OrsoEric/robot-ros2-Industrious-Resonance/Images/2025-08-23_08_58_IMG_20250823_085845.jpg

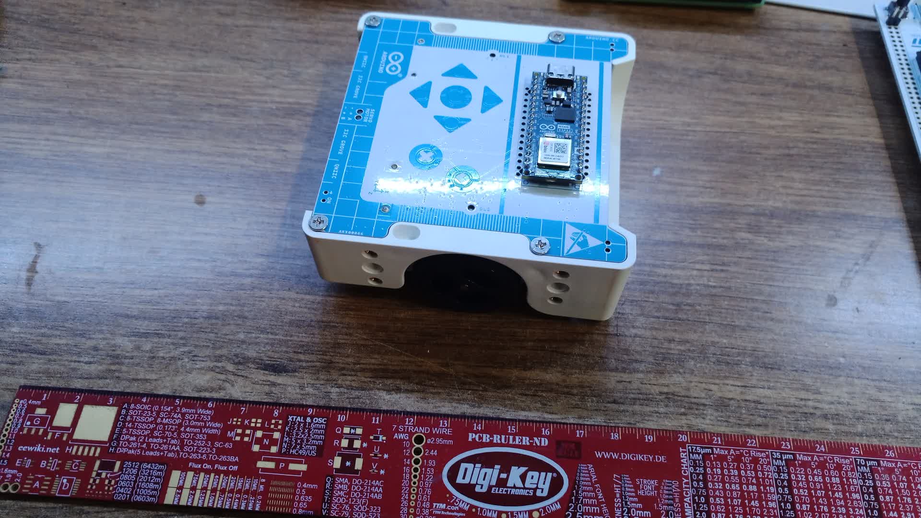
Images/2025-08-23_08_58_IMG_20250823_085845.jpg
