OrsoEric/robot-ros2-Industrious-Resonance/Images/2025-08-23_09_10_IMG_20250823_091027.jpg

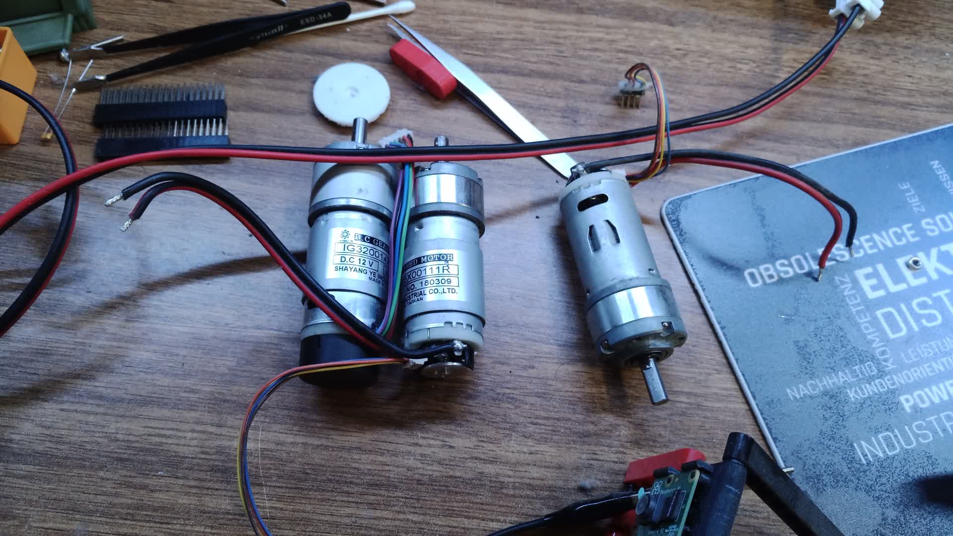
Images/2025-08-23_09_10_IMG_20250823_091027.jpg
