OrsoEric/robot-ros2-Industrious-Resonance/Images/2025-08-23_09_23_IMG_20250823_092340.jpg

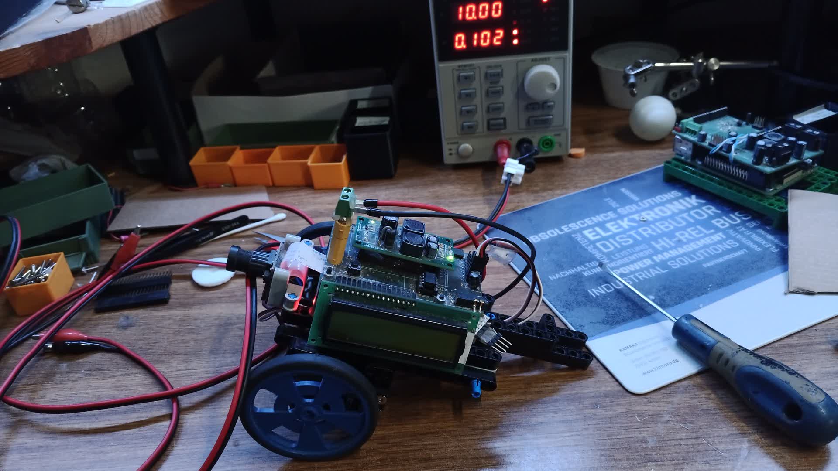
Images/2025-08-23_09_23_IMG_20250823_092340.jpg
