OrsoEric/robot-ros2-Industrious-Resonance/Images/2025-08-23_10_18_IMG_20250823_101841.jpg

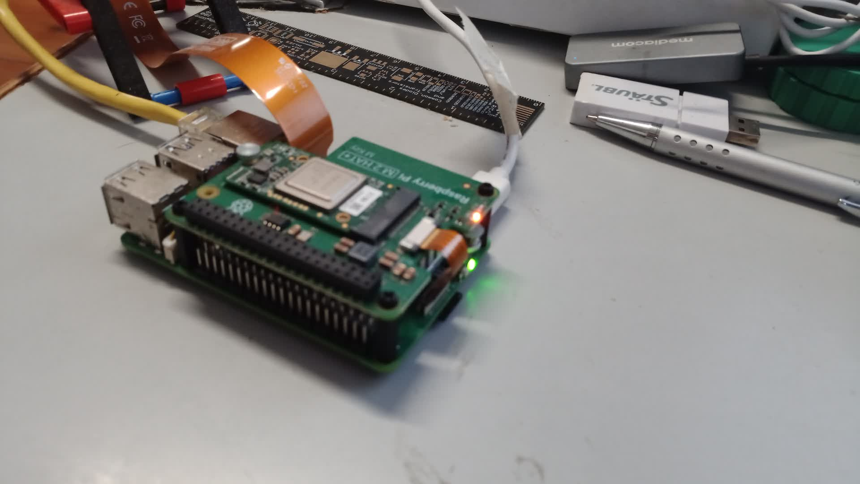
Images/2025-08-23_10_18_IMG_20250823_101841.jpg
