OrsoEric/robot-ros2-Industrious-Resonance/Images/2025-08-23_10_36_IMG_20250823_103639.jpg

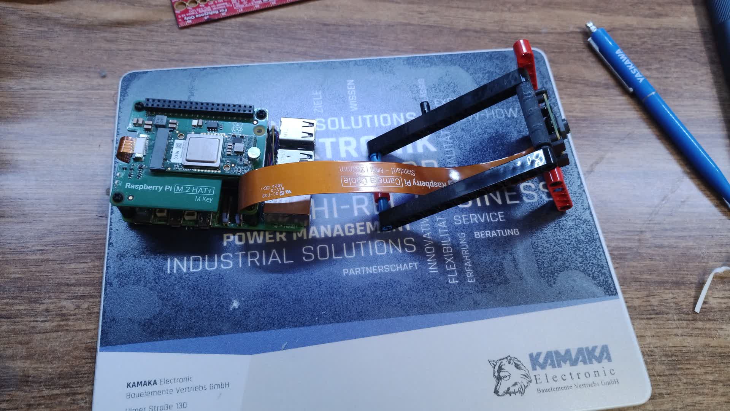
Images/2025-08-23_10_36_IMG_20250823_103639.jpg
