OrsoEric/robot-ros2-Industrious-Resonance/Images/2025-08-23_10_53_IMG_20250823_105316.jpg

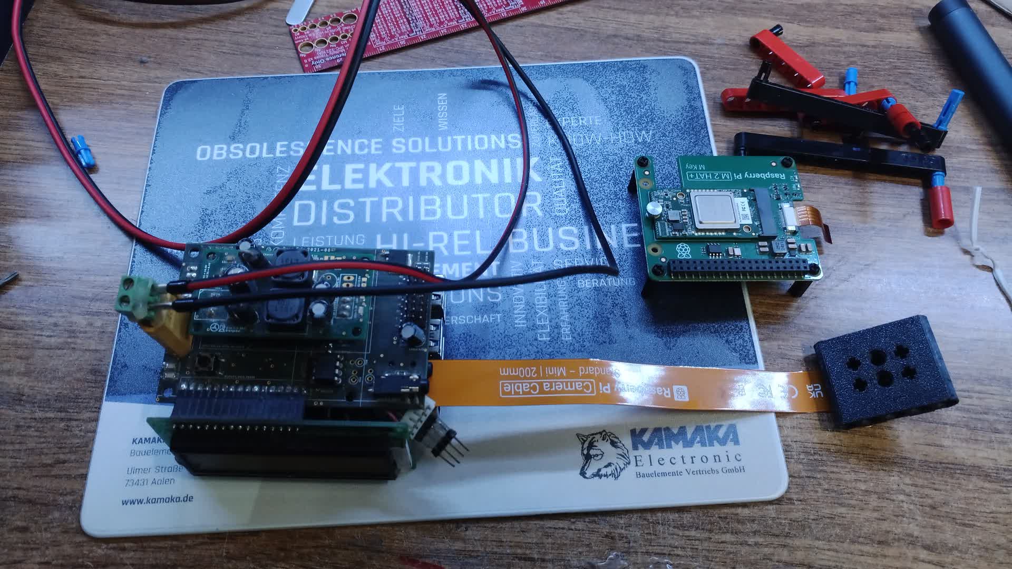
Images/2025-08-23_10_53_IMG_20250823_105316.jpg
