OrsoEric/robot-ros2-Industrious-Resonance/Images/2025-08-25_19_26_IMG_20250825_192647.jpg

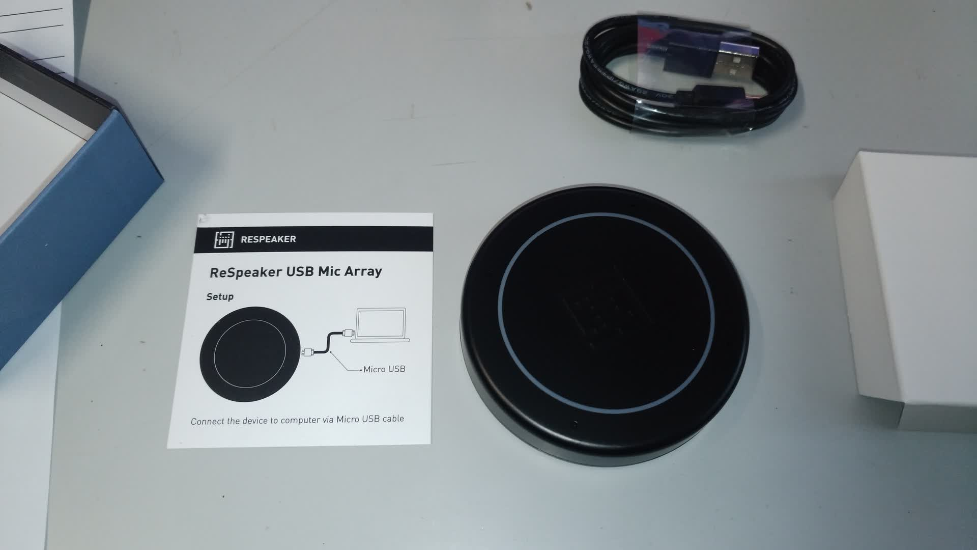
Images/2025-08-25_19_26_IMG_20250825_192647.jpg
