OrsoEric/robot-ros2-Industrious-Resonance/Images/2025-08-27_08_57_IMG_20250827_085710.jpg

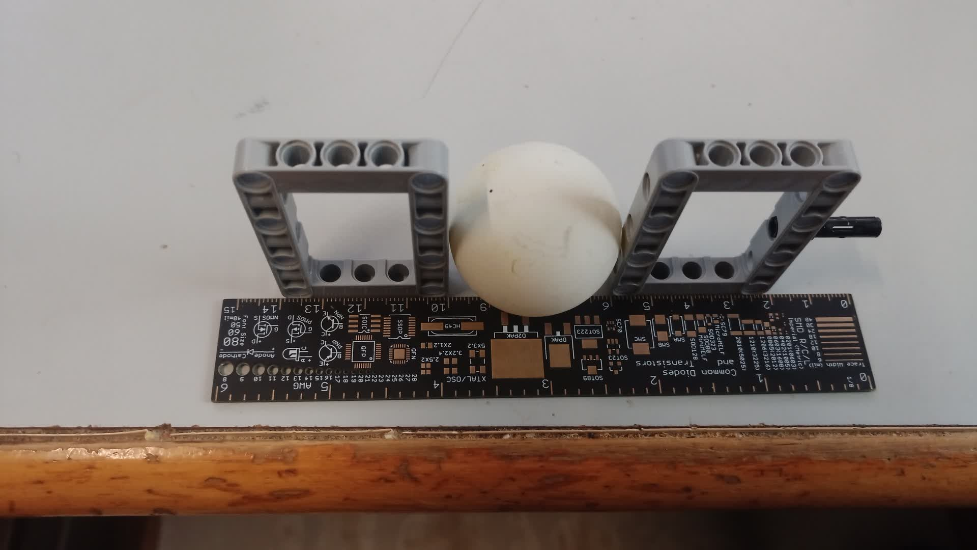
Images/2025-08-27_08_57_IMG_20250827_085710.jpg
