OrsoEric/robot-ros2-Industrious-Resonance/Images/2025-08-27_13_16_IMG_20250827_131654.jpg

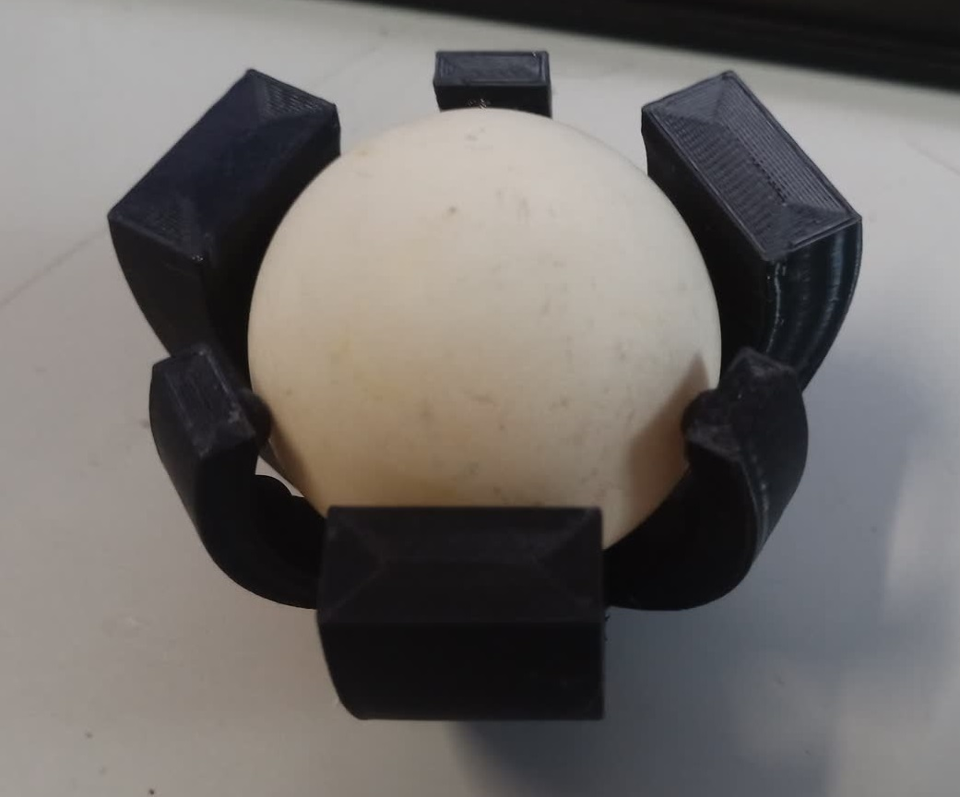
Images/2025-08-27_13_16_IMG_20250827_131654.jpg
