OrsoEric/robot-ros2-Industrious-Resonance/Images/2025-08-27_14_06_IMG_20250827_140644.jpg

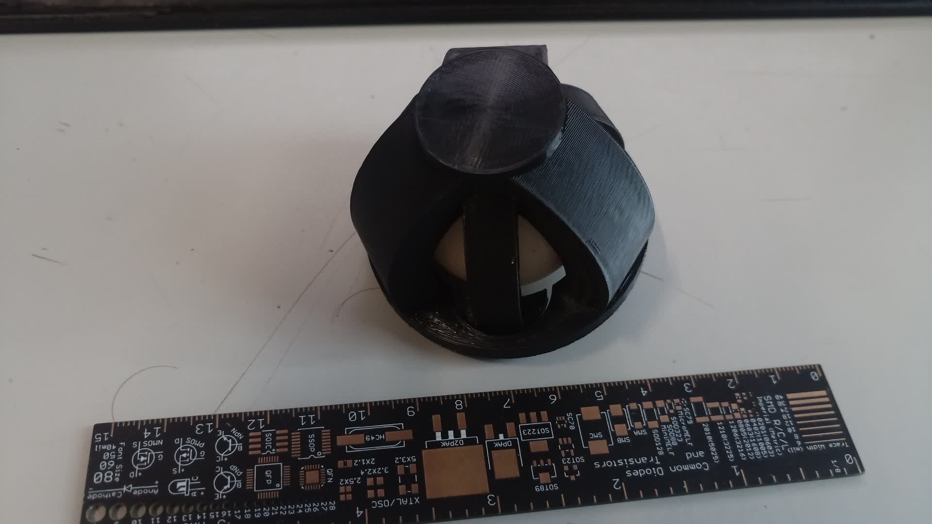
Images/2025-08-27_14_06_IMG_20250827_140644.jpg
