OrsoEric/robot-ros2-Industrious-Resonance/Images/2025-08-27_16_06_IMG_20250827_160652.jpg

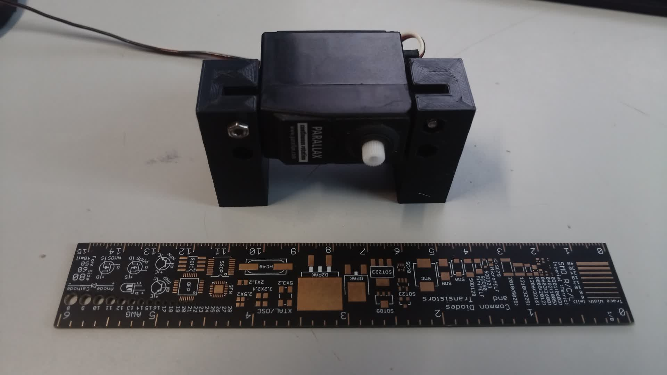
Images/2025-08-27_16_06_IMG_20250827_160652.jpg
