OrsoEric/robot-ros2-Industrious-Resonance/Images/2025-08-27_17_10_IMG_20250827_171056.jpg

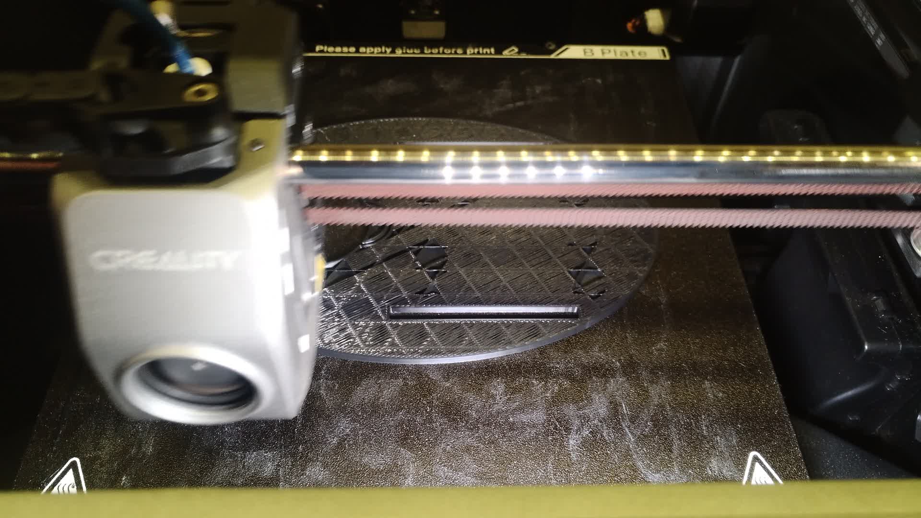
Images/2025-08-27_17_10_IMG_20250827_171056.jpg
