OrsoEric/robot-ros2-Industrious-Resonance/Images/2025-08-27_17_11_IMG_20250827_171102.jpg

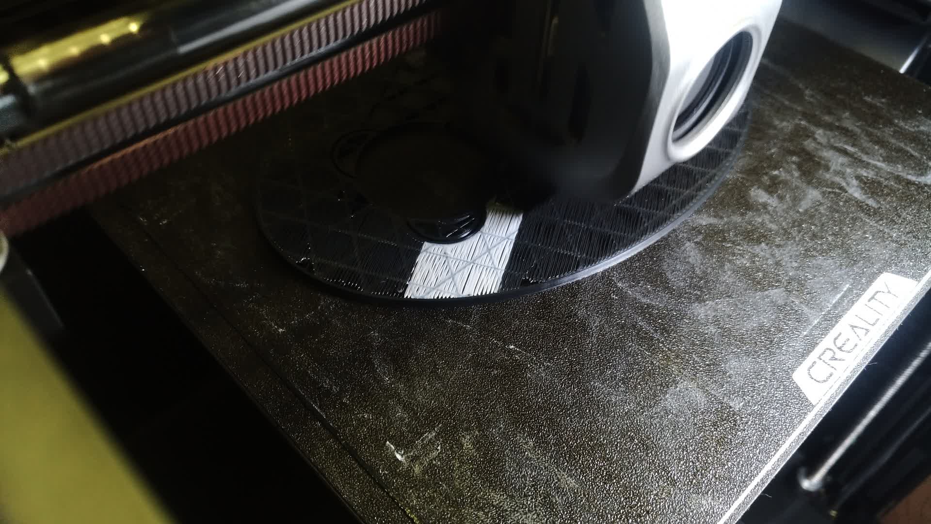
Images/2025-08-27_17_11_IMG_20250827_171102.jpg
