OrsoEric/robot-ros2-Industrious-Resonance/Images/2025-11-06_13_21_IMG_20251106_132114.jpg

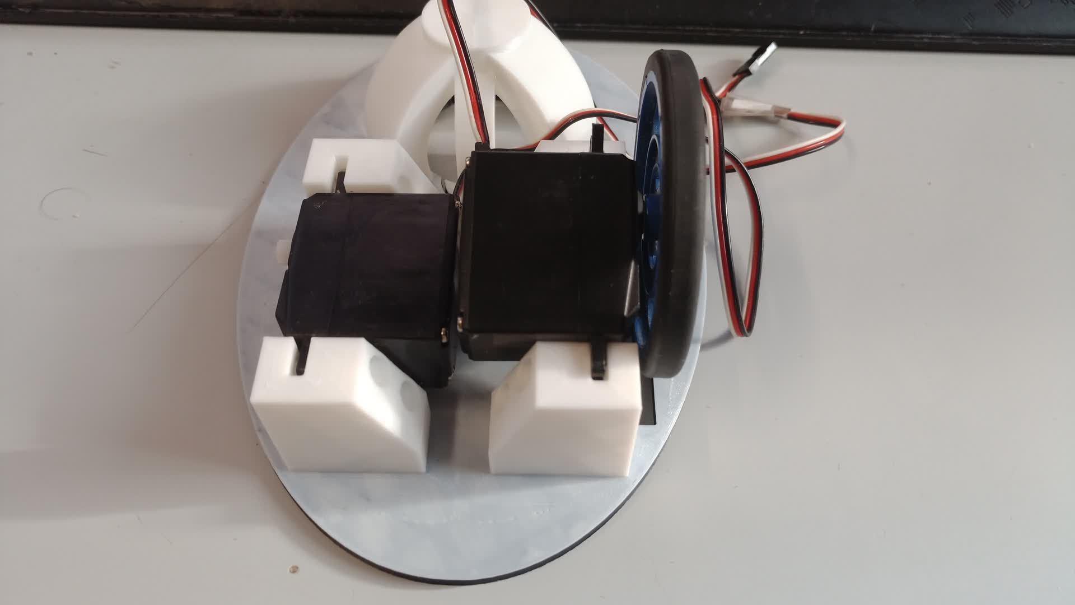
Images/2025-11-06_13_21_IMG_20251106_132114.jpg
