OrsoEric/robot-ros2-Industrious-Resonance/Images/2025-11-06_17_39_IMG_20251106_173956.jpg

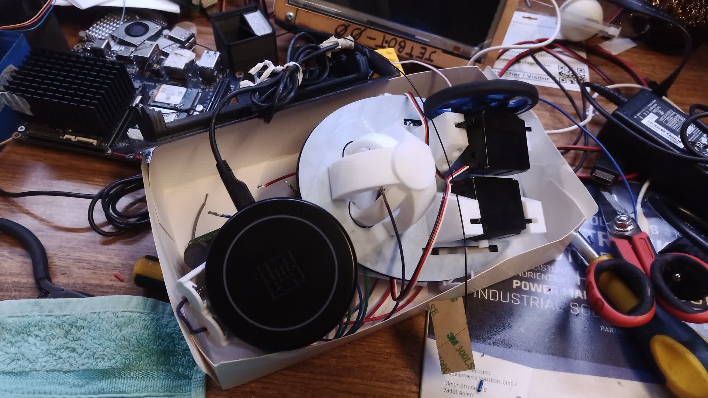
Images/2025-11-06_17_39_IMG_20251106_173956.jpg
