OrsoEric/robot-ros2-Industrious-Resonance/Images/2025-11-08_11_53_IMG_20251108_115348.jpg

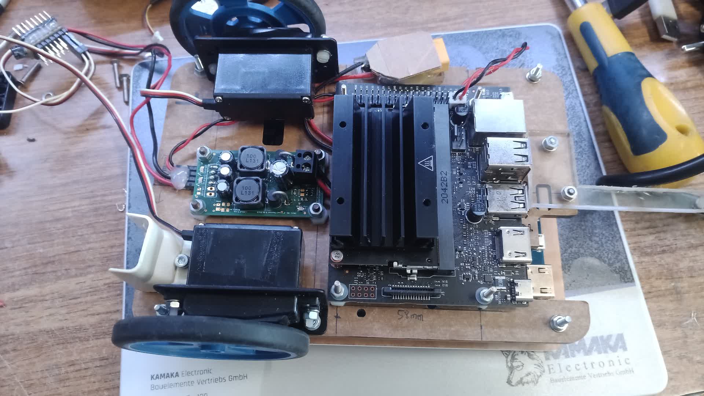
Images/2025-11-08_11_53_IMG_20251108_115348.jpg
