OrsoEric/robot-ros2-Industrious-Resonance/Images/2025-11-08_12_08_IMG_20251108_120841.jpg

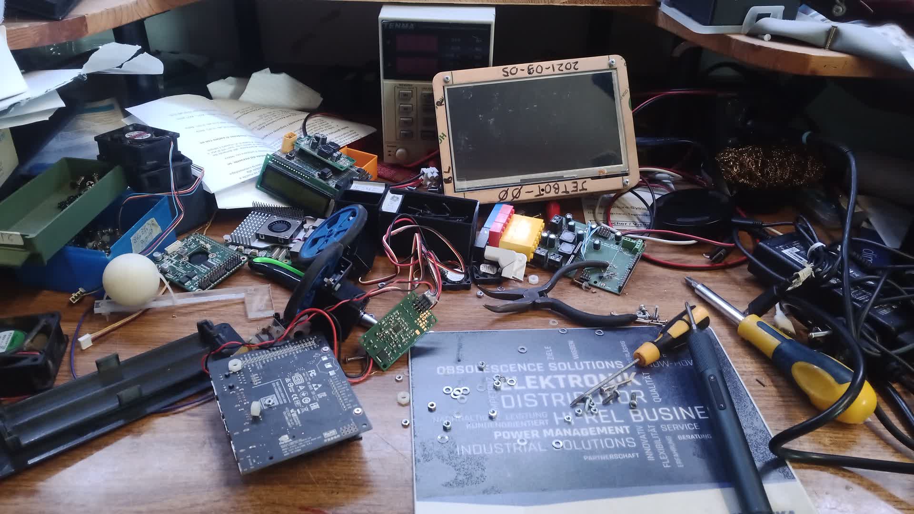
Images/2025-11-08_12_08_IMG_20251108_120841.jpg
