OrsoEric/robot-ros2-Industrious-Resonance/Images/2025-11-08_12_09_IMG_20251108_120904.jpg

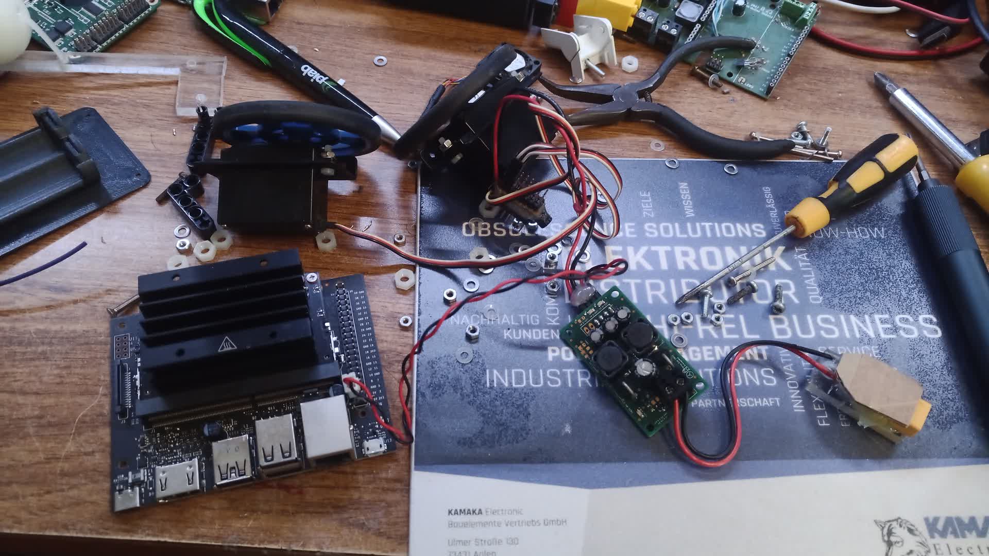
Images/2025-11-08_12_09_IMG_20251108_120904.jpg
