OrsoEric/robot-ros2-Industrious-Resonance/Images/2025-11-08_12_16_IMG_20251108_121650.jpg

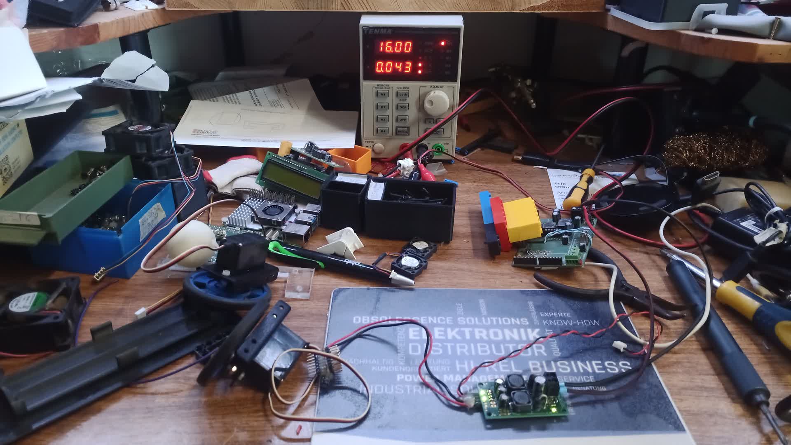
Images/2025-11-08_12_16_IMG_20251108_121650.jpg
