OrsoEric/robot-ros2-Industrious-Resonance/Images/2025-11-08_12_21_IMG_20251108_122142.jpg

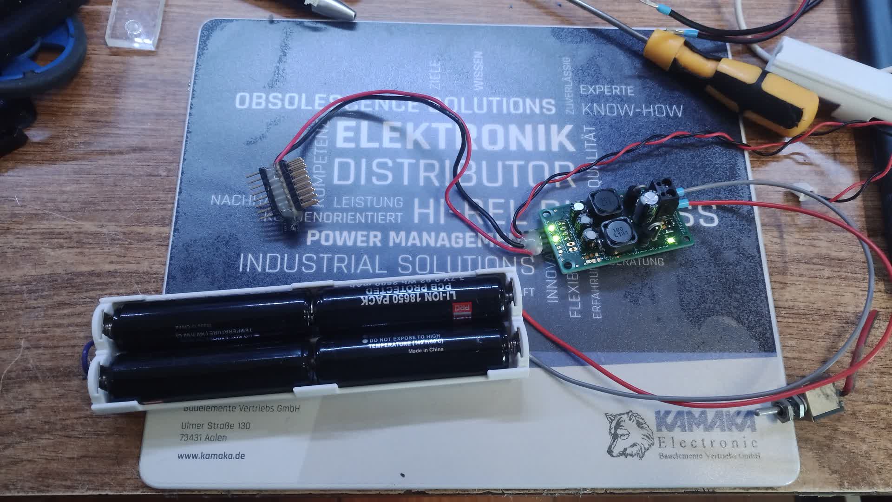
Images/2025-11-08_12_21_IMG_20251108_122142.jpg
