OrsoEric/robot-ros2-Industrious-Resonance/Images/2025-11-08_21_04_IMG_20251108_210415.jpg

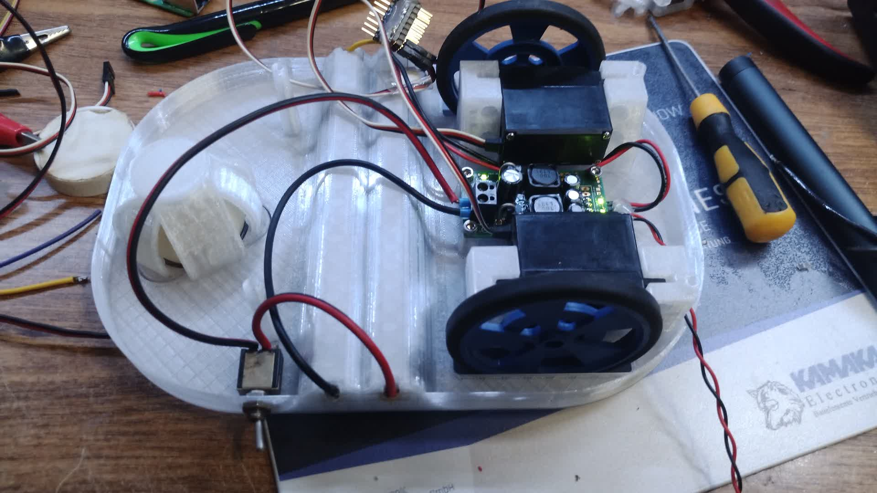
Images/2025-11-08_21_04_IMG_20251108_210415.jpg
