OrsoEric/robot-ros2-Industrious-Resonance/Images/2025-11-08_21_04_IMG_20251108_210431.jpg

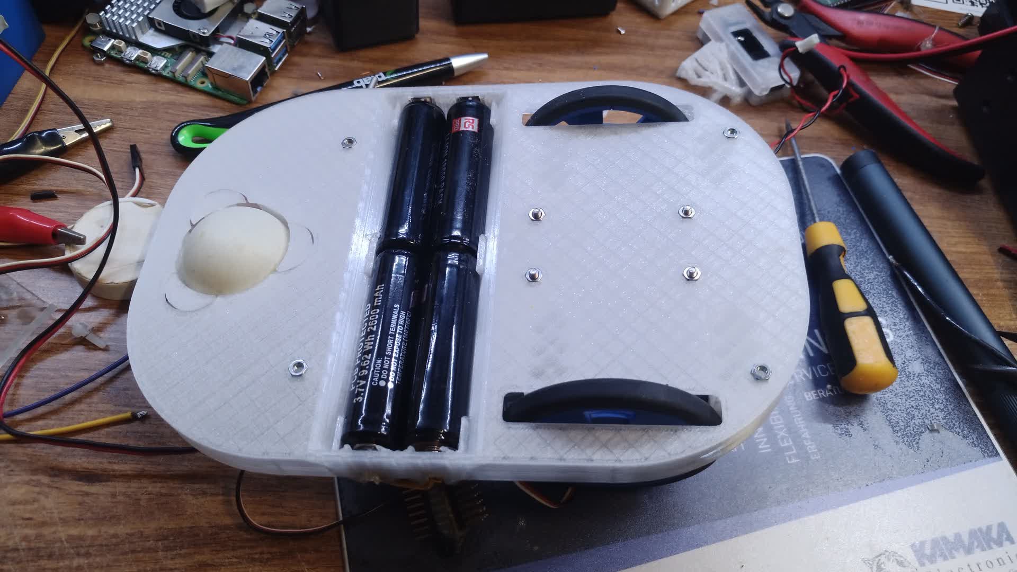
Images/2025-11-08_21_04_IMG_20251108_210431.jpg
