OrsoEric/robot-ros2-Industrious-Resonance/Images/2025-11-09_09_07_IMG_20251109_090746.jpg

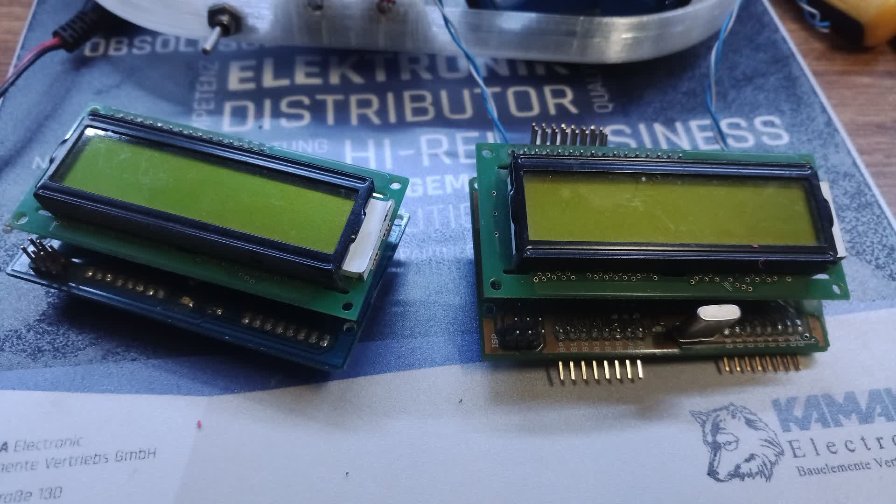
Images/2025-11-09_09_07_IMG_20251109_090746.jpg
