OrsoEric/robot-ros2-Industrious-Resonance/Images/2025-11-09_09_24_IMG_20251109_092415.jpg

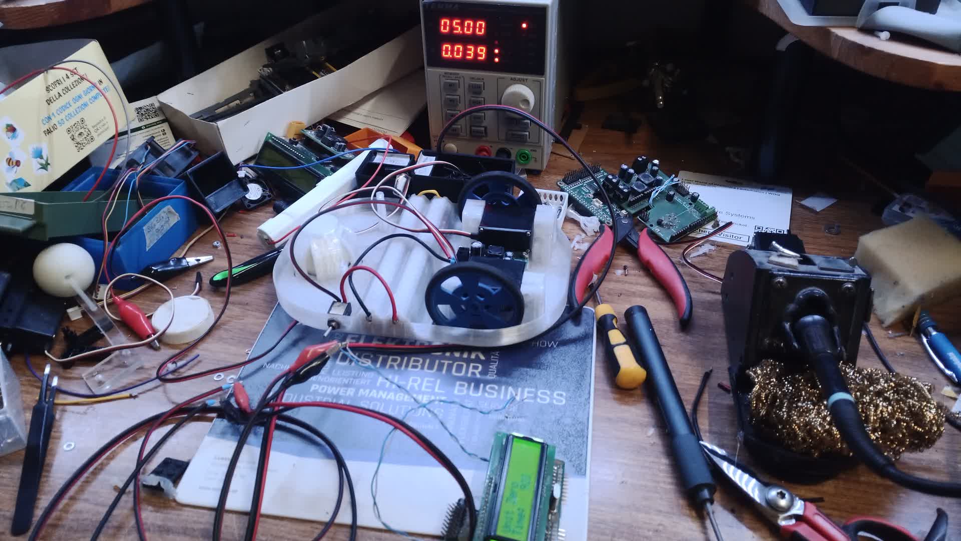
Images/2025-11-09_09_24_IMG_20251109_092415.jpg
