OrsoEric/robot-ros2-Industrious-Resonance/Images/2025-11-09_09_36_IMG_20251109_093618.jpg

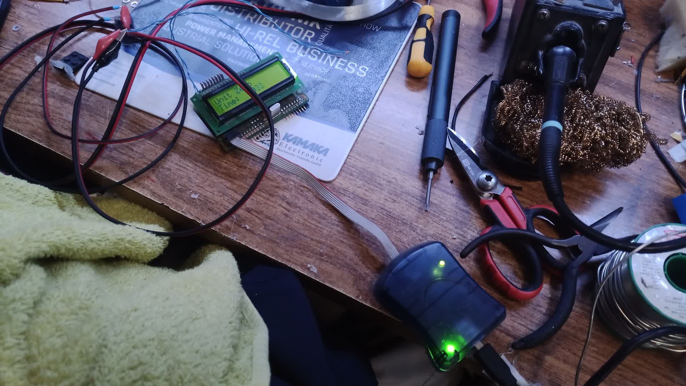
Images/2025-11-09_09_36_IMG_20251109_093618.jpg
