OrsoEric/robot-ros2-Industrious-Resonance/Images/2025-11-09_09_51_IMG_20251109_095159.jpg

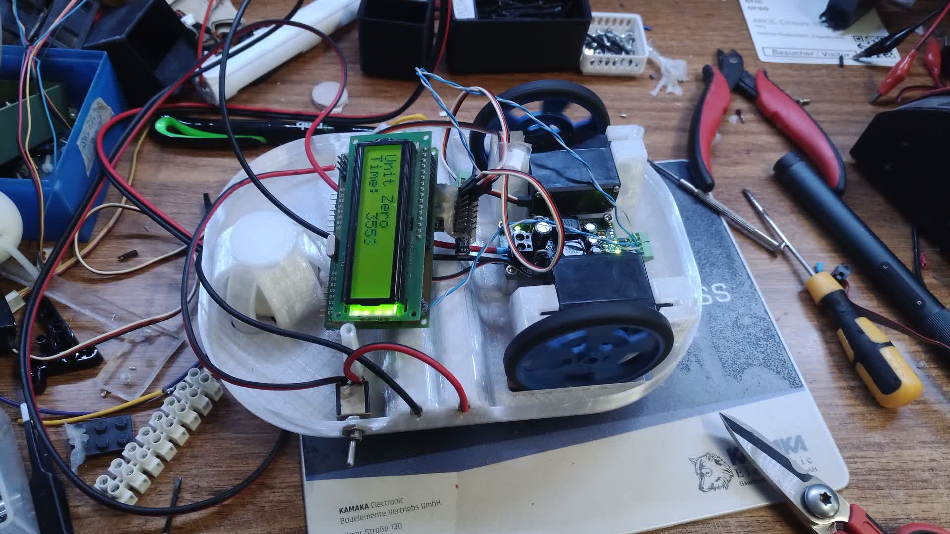
Images/2025-11-09_09_51_IMG_20251109_095159.jpg
