OrsoEric/robot-ros2-Industrious-Resonance/Images/2025-11-09_11_59_IMG_20251109_115955.jpg

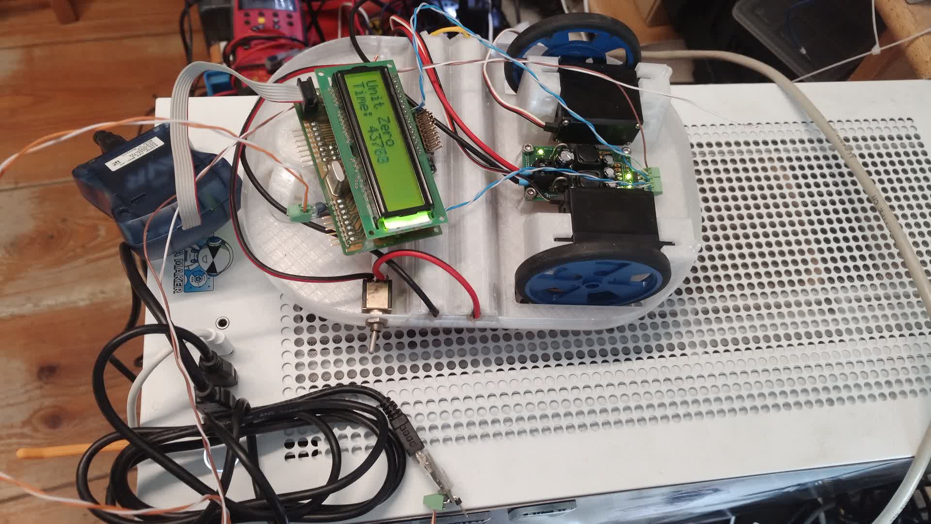
Images/2025-11-09_11_59_IMG_20251109_115955.jpg
