OrsoEric/robot-ros2-Industrious-Resonance/Images/2025-11-09_13_45_IMG_20251109_134523.jpg

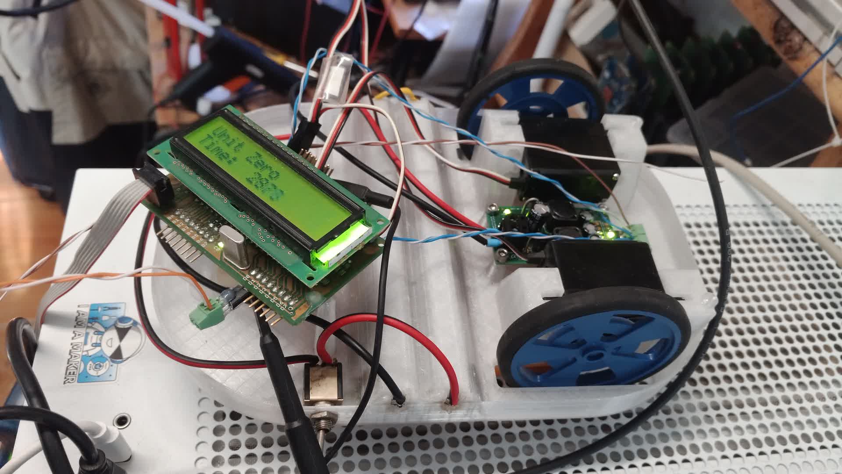
Images/2025-11-09_13_45_IMG_20251109_134523.jpg
