OrsoEric/robot-ros2-Industrious-Resonance/Images/IMG_20250823_113036.jpg

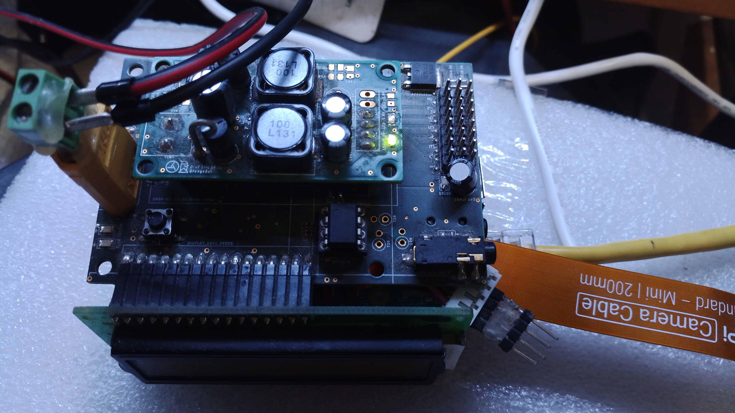
Images/IMG_20250823_113036.jpg
