OrsoEric/robot-ros2-Industrious-Resonance/Images/Screenshot 2025-08-27 132716.png

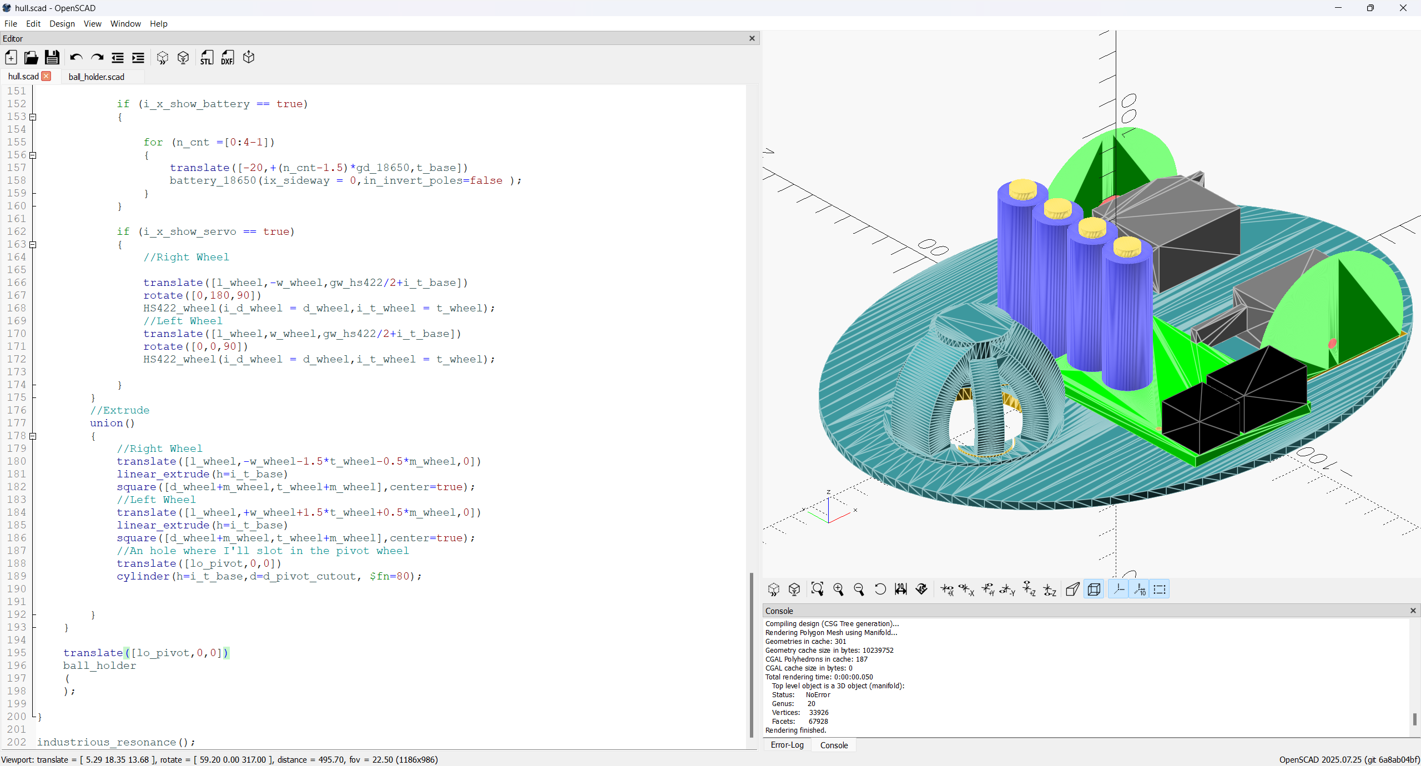
Images/Screenshot 2025-08-27 132716.png
