OrsoEric/robot-ros2-Industrious-Resonance/Images/Screenshot 2025-10-25 123542.png

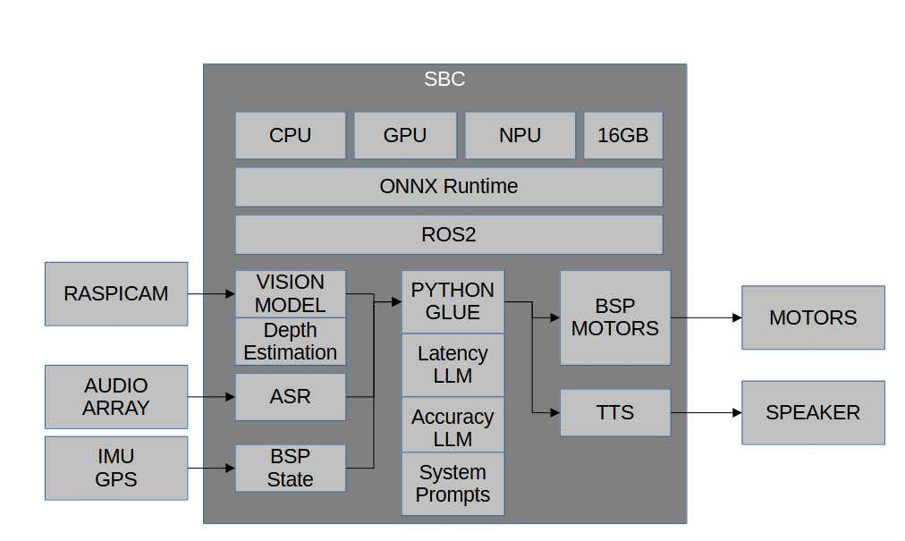
Images/Screenshot 2025-10-25 123542.png
