OrsoEric/robot-ros2-Industrious-Resonance/Images/Screenshot 2025-11-02 103534.png

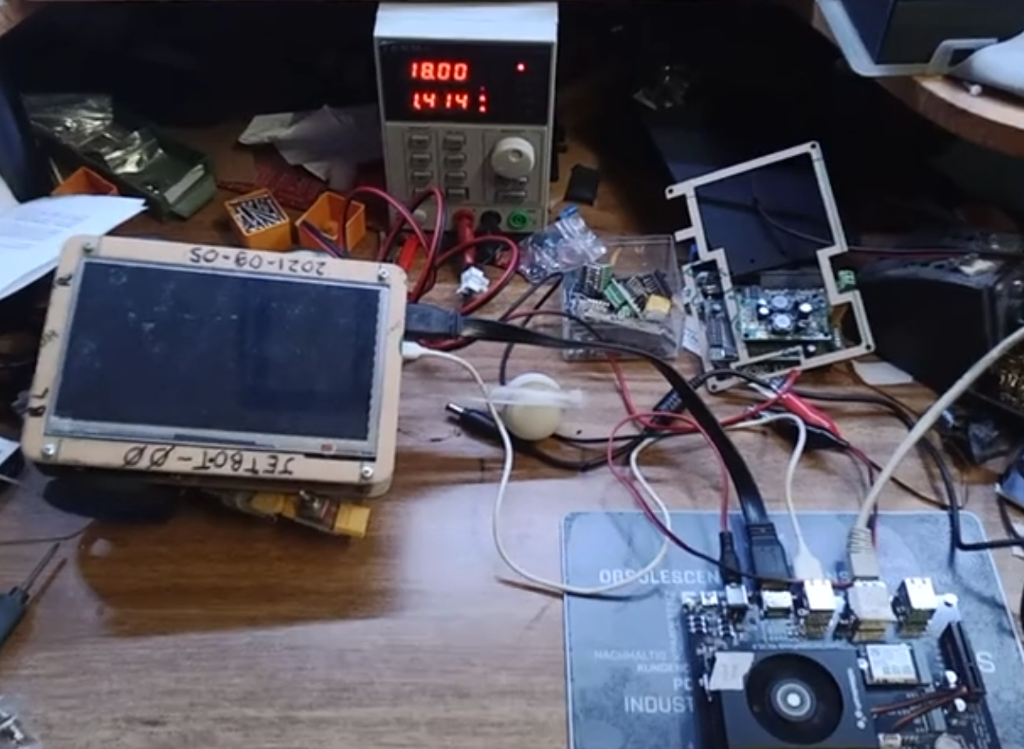
Images/Screenshot 2025-11-02 103534.png
