OrsoEric/robot-ros2-Industrious-Resonance/Images/Screenshot 2025-11-06 130414.png

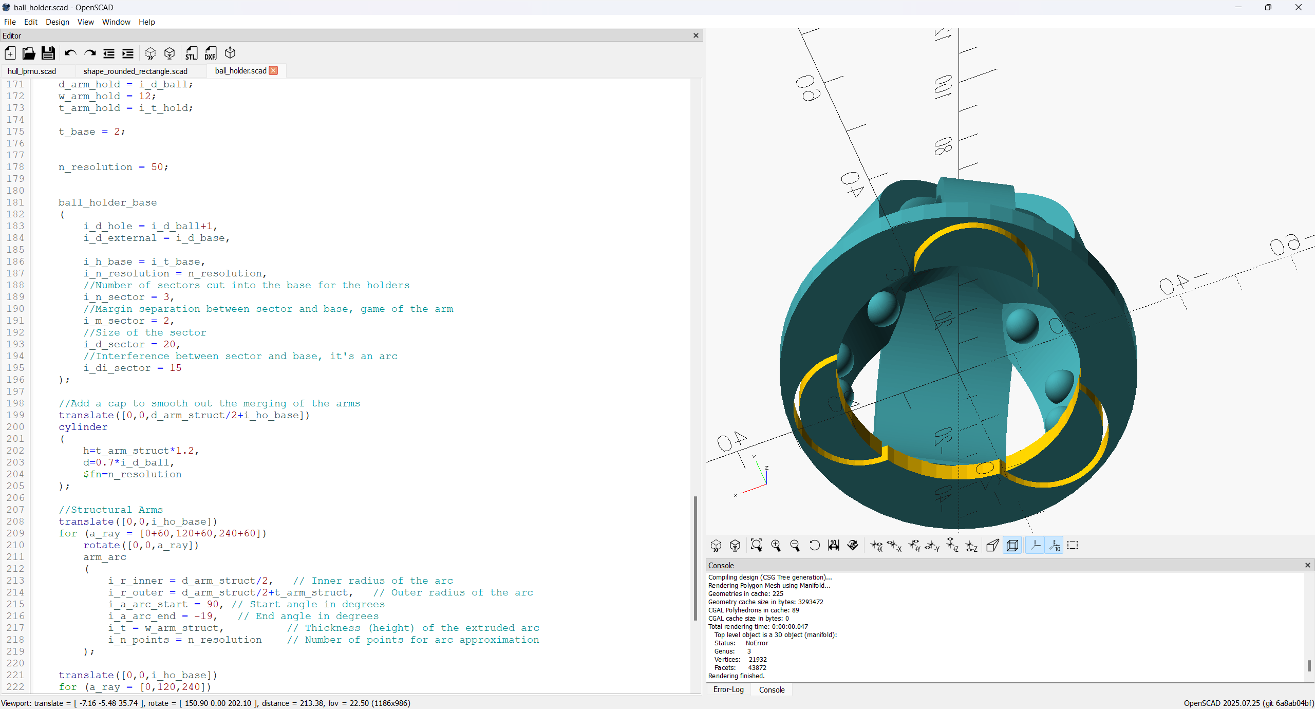
Images/Screenshot 2025-11-06 130414.png
