OrsoEric/robot-ros2-Industrious-Resonance/Images/Screenshot 2025-11-06 132450.png

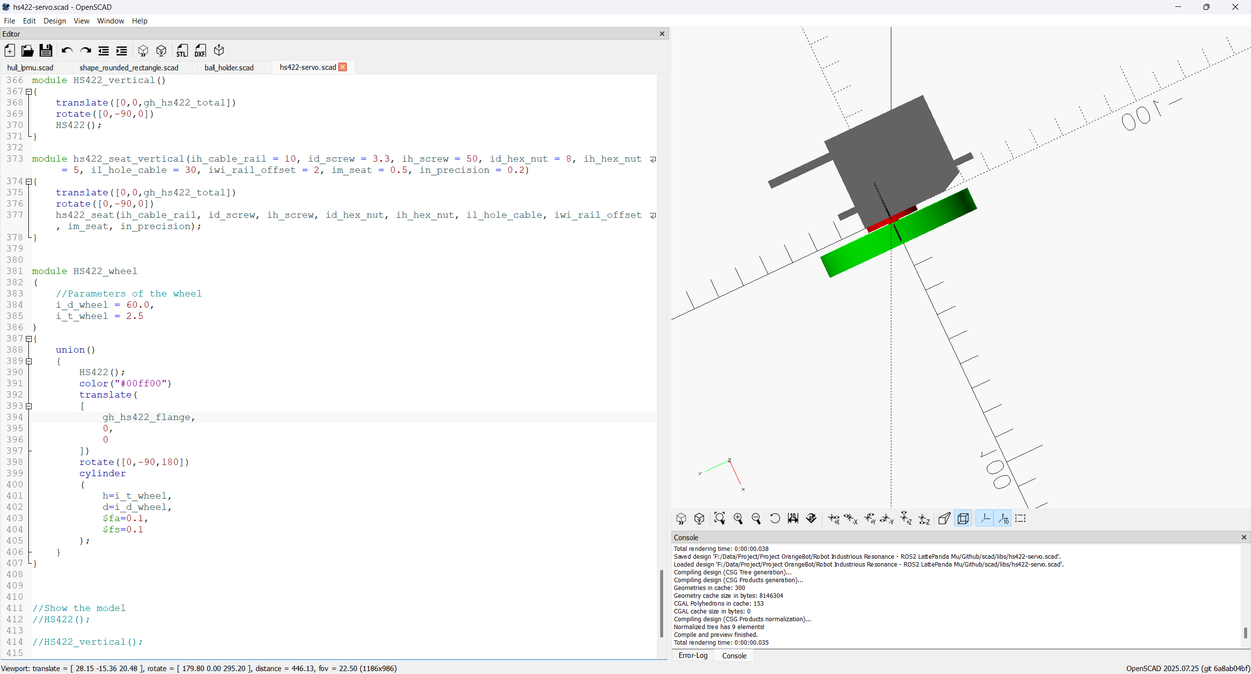
Images/Screenshot 2025-11-06 132450.png
