OrsoEric/robot-ros2-Industrious-Resonance/Images/Screenshot 2025-11-08 085803.png

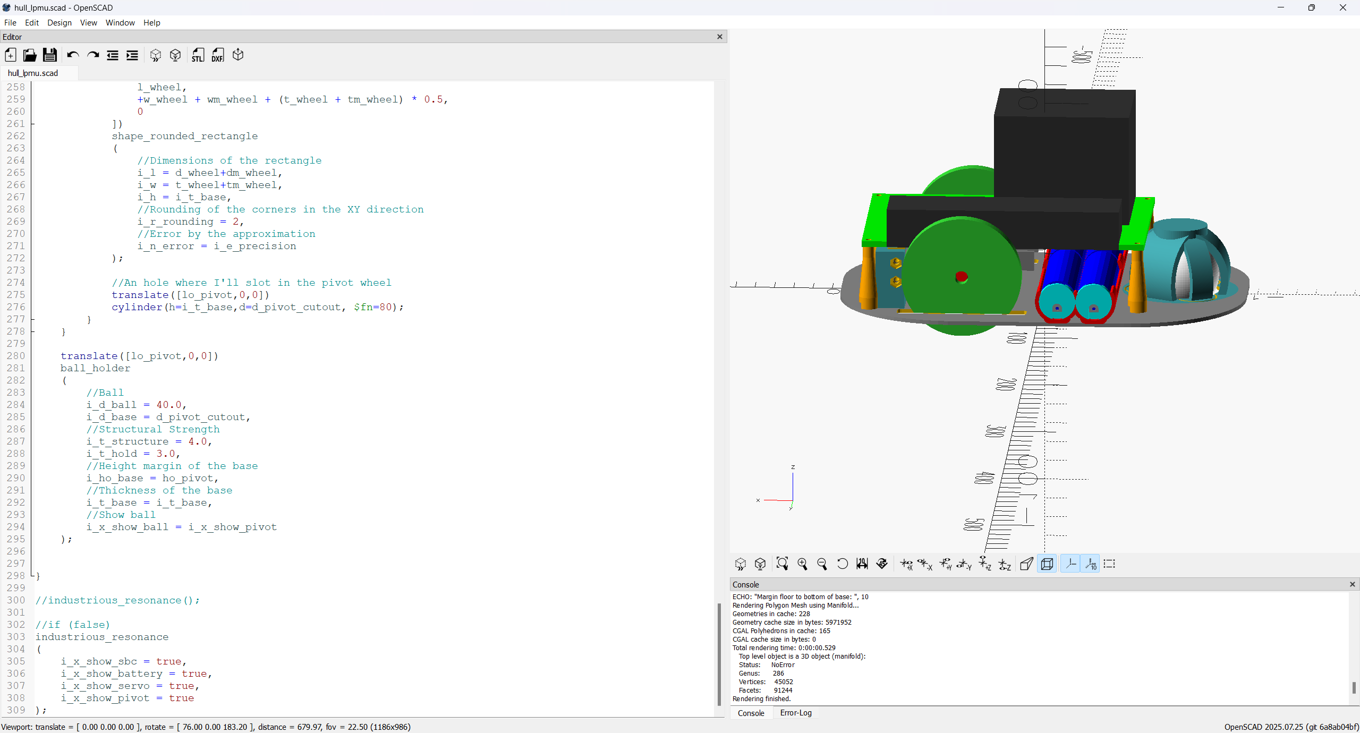
Images/Screenshot 2025-11-08 085803.png
