OrsoEric/robot-ros2-Industrious-Resonance/Images/Screenshot 2025-11-08 110413.png

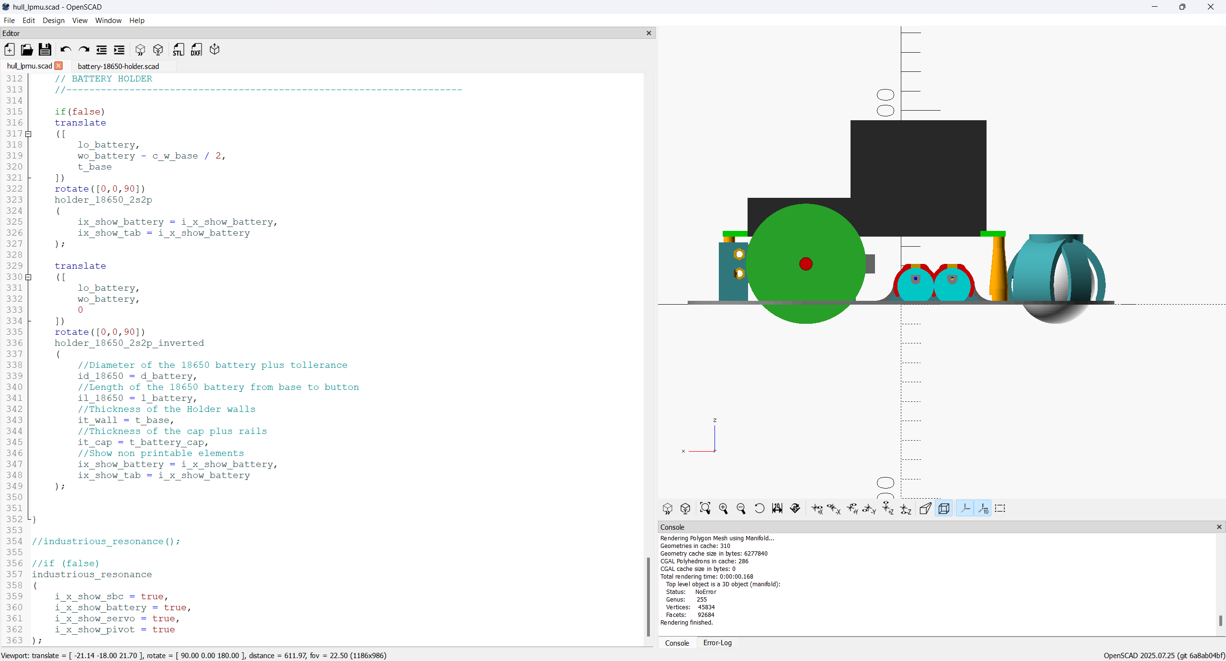
Images/Screenshot 2025-11-08 110413.png
