OrsoEric/robot-ros2-Industrious-Resonance/Images/Screenshot 2025-11-08 111840.png

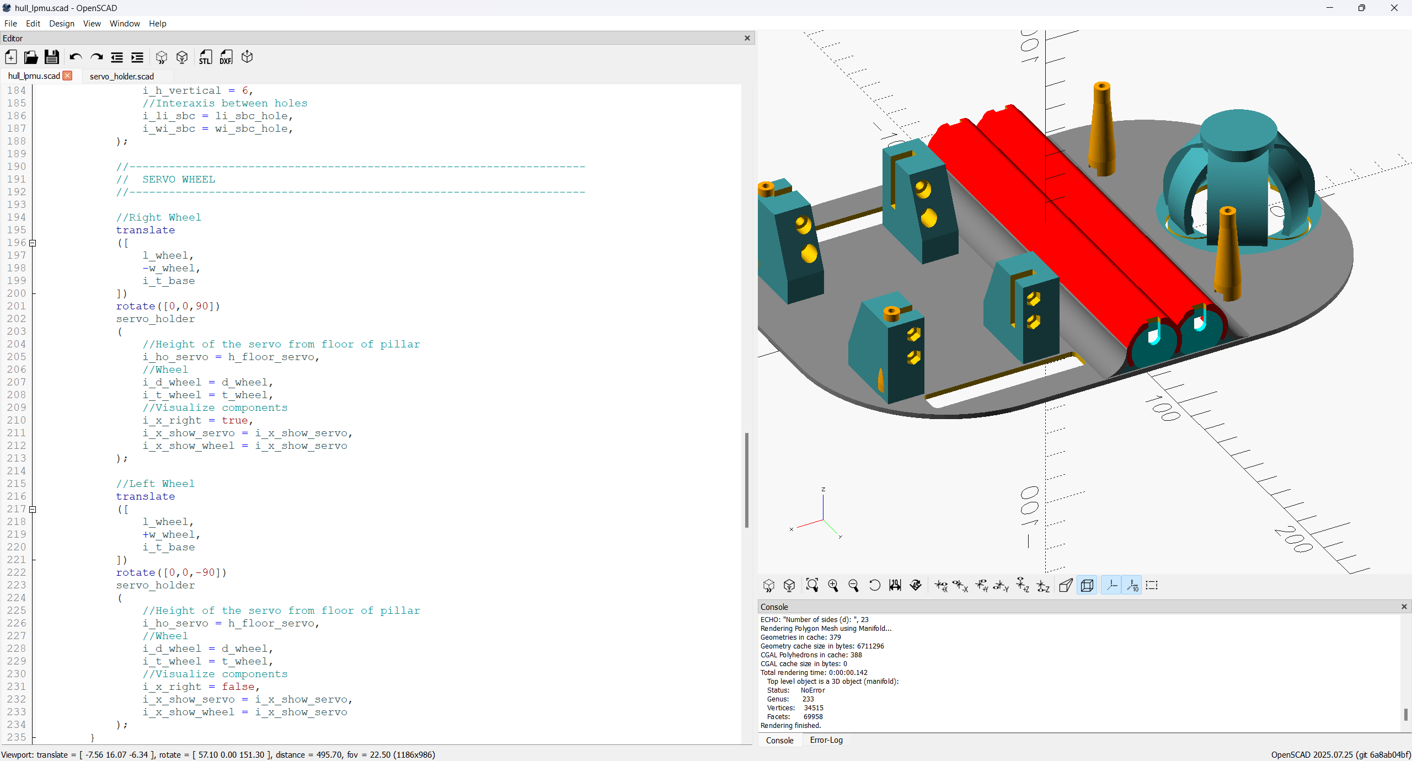
Images/Screenshot 2025-11-08 111840.png
