OrsoEric/robot-ros2-Industrious-Resonance/Images/Screenshot 2025-11-08 131336.png

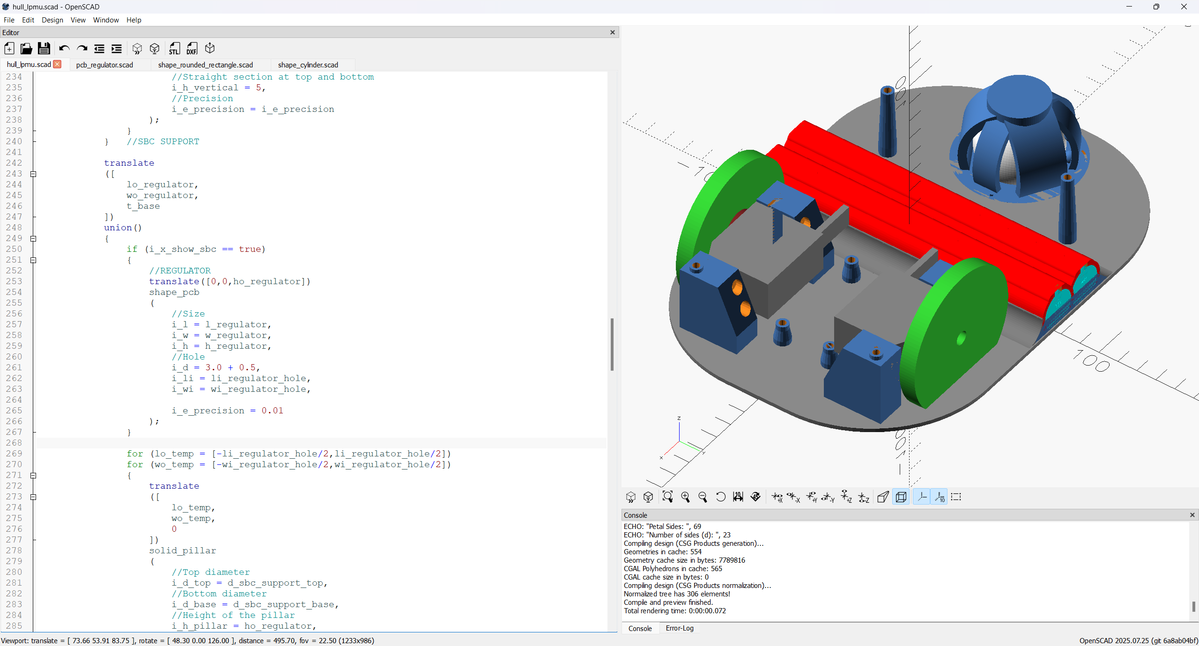
Images/Screenshot 2025-11-08 131336.png
