OrsoEric/robot-ros2-Industrious-Resonance/Images/Screenshot 2025-11-08 135248.png

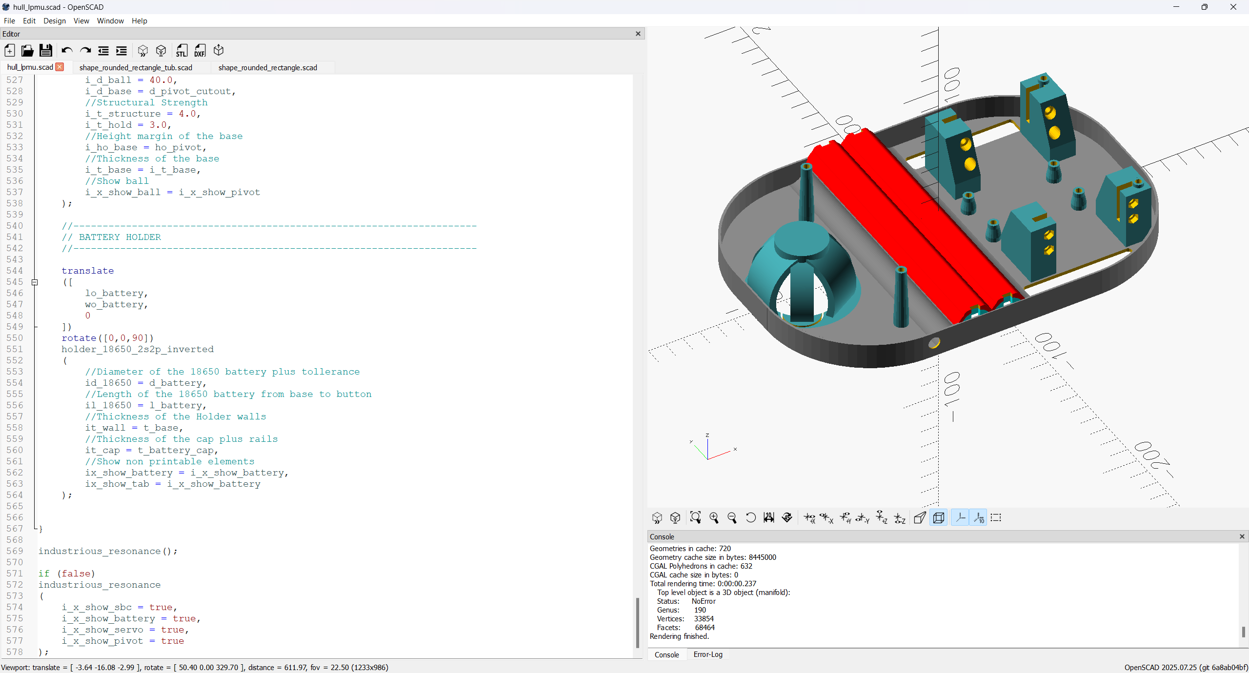
Images/Screenshot 2025-11-08 135248.png
