OrsoEric/robot-ros2-Industrious-Resonance/Images/Screenshot 2025-11-09 075105.png

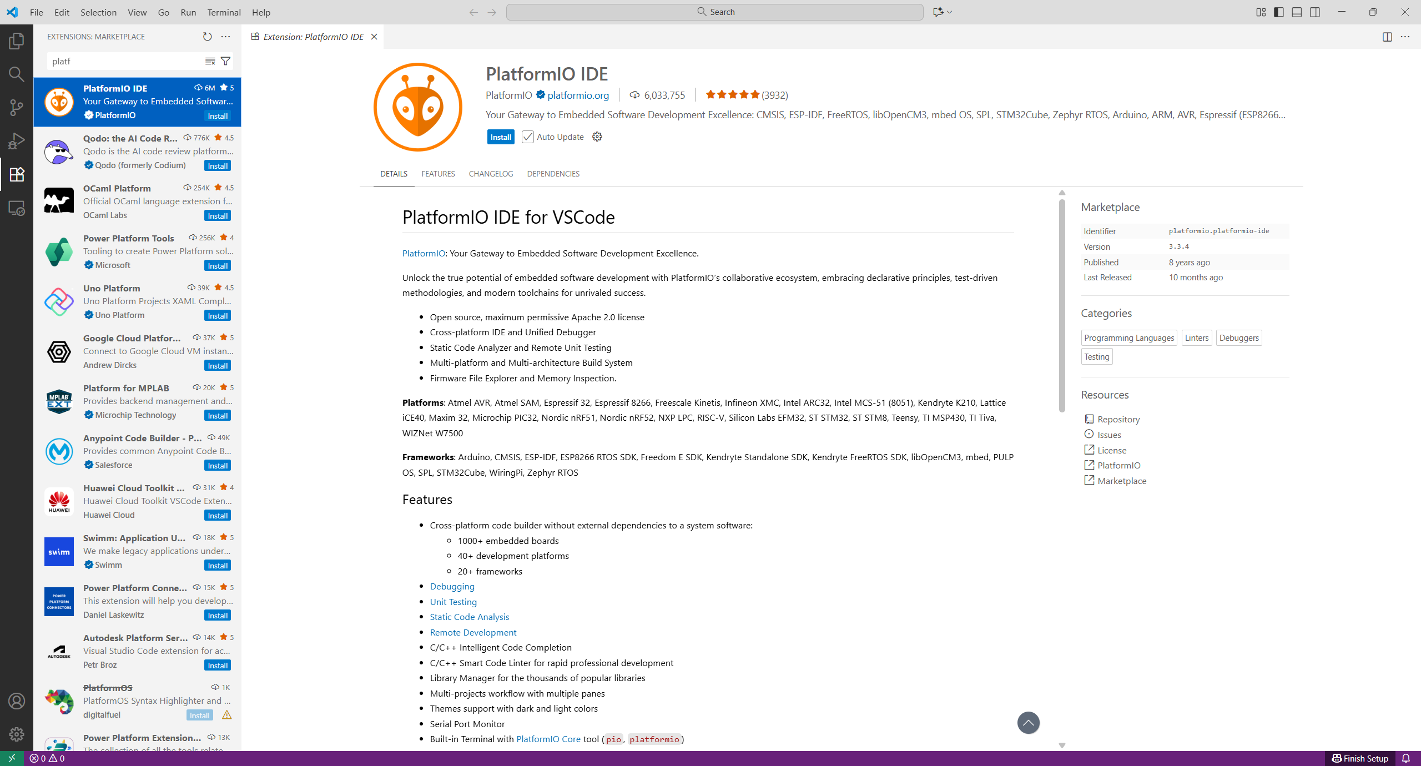
Images/Screenshot 2025-11-09 075105.png
