OrsoEric/robot-ros2-Industrious-Resonance/Images/Screenshot 2025-11-09 091956.png

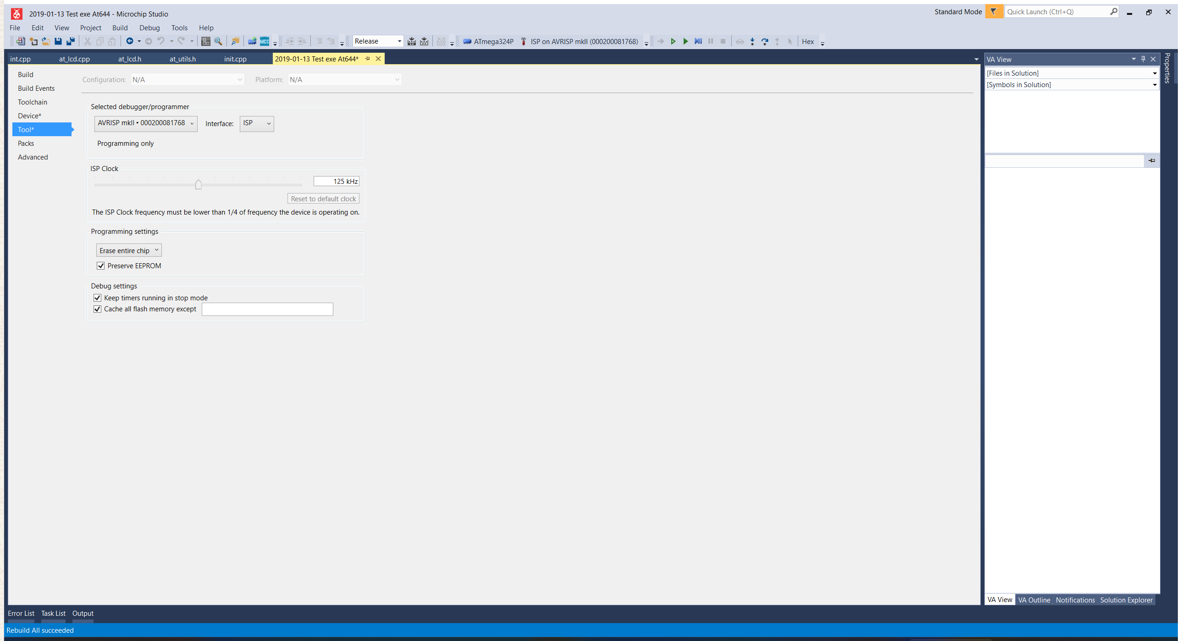
Images/Screenshot 2025-11-09 091956.png
