OrsoEric/robot-ros2-Industrious-Resonance/Images/Screenshot 2025-11-09 092602.png

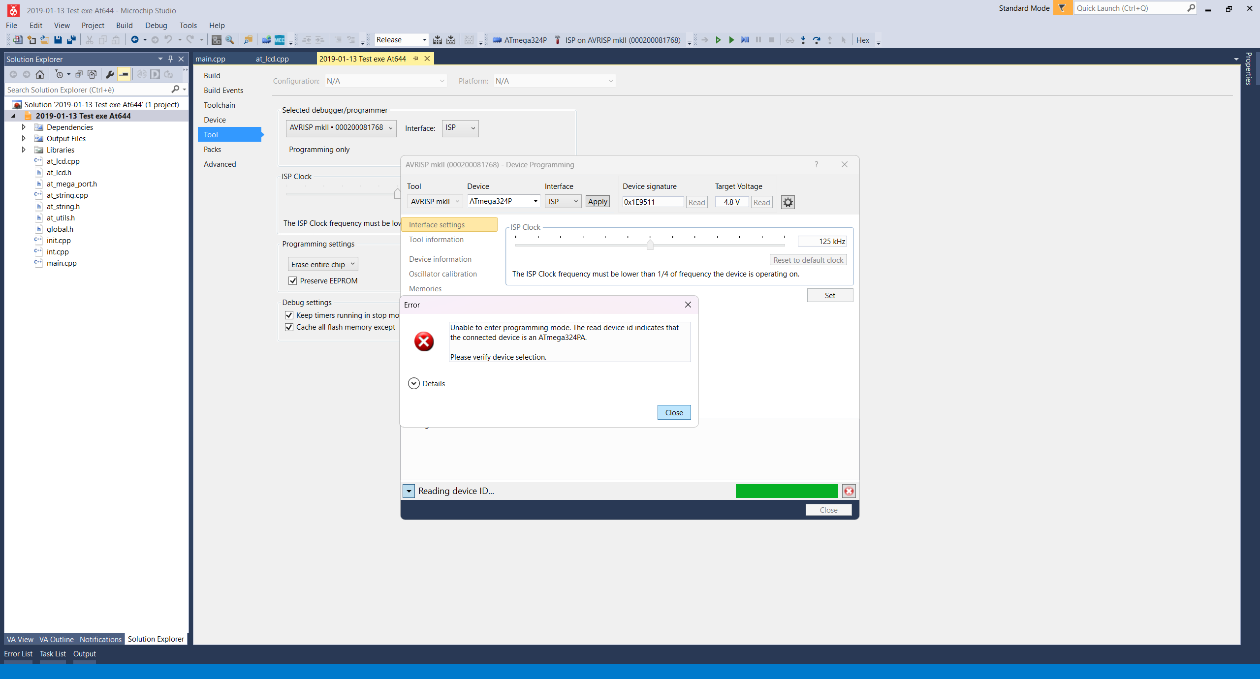
Images/Screenshot 2025-11-09 092602.png
