OrsoEric/robot-ros2-Industrious-Resonance/Images/Screenshot 2025-11-09 120735.png

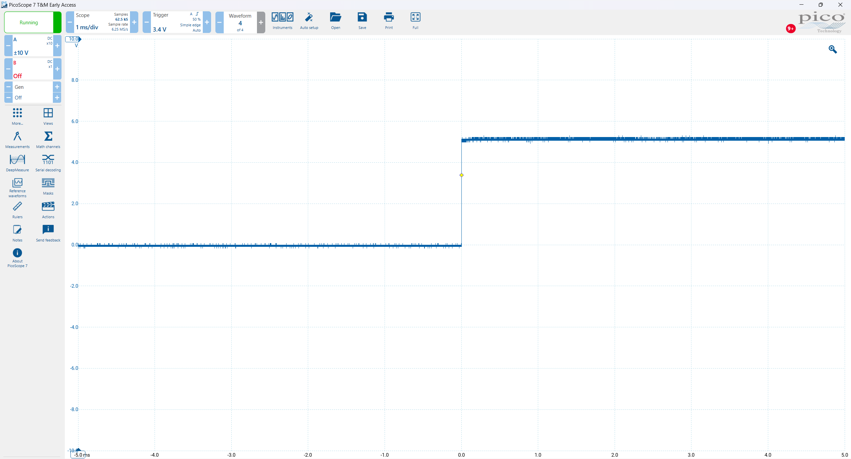
Images/Screenshot 2025-11-09 120735.png
