OrsoEric/robot-ros2-Industrious-Resonance/Images/Screenshot (1).png

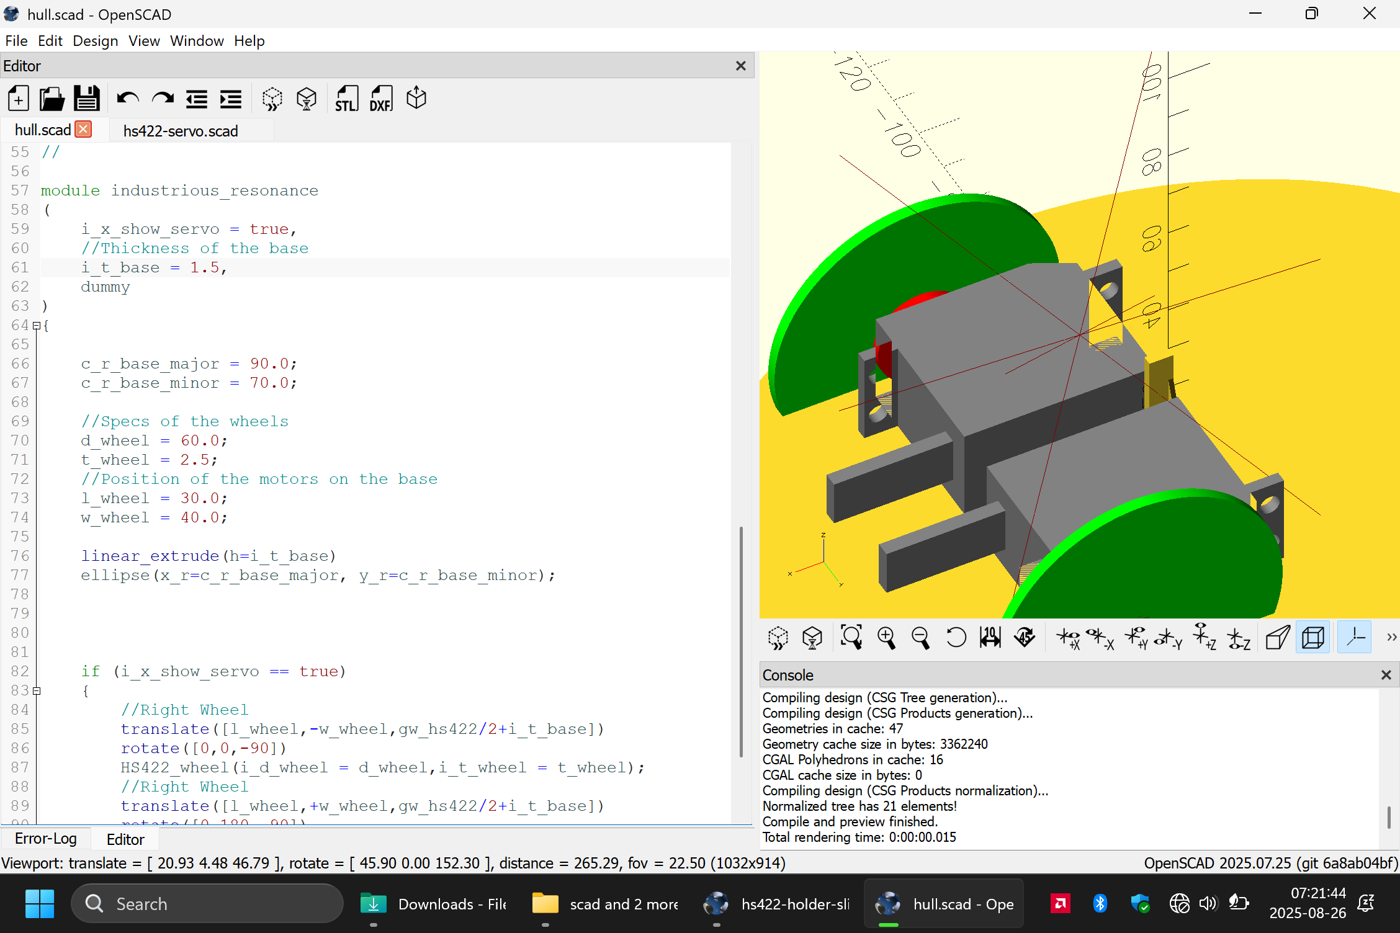
Images/Screenshot (1).png
