OrsoEric/robot-ros2-Industrious-Resonance/Images/Screenshot (3).png

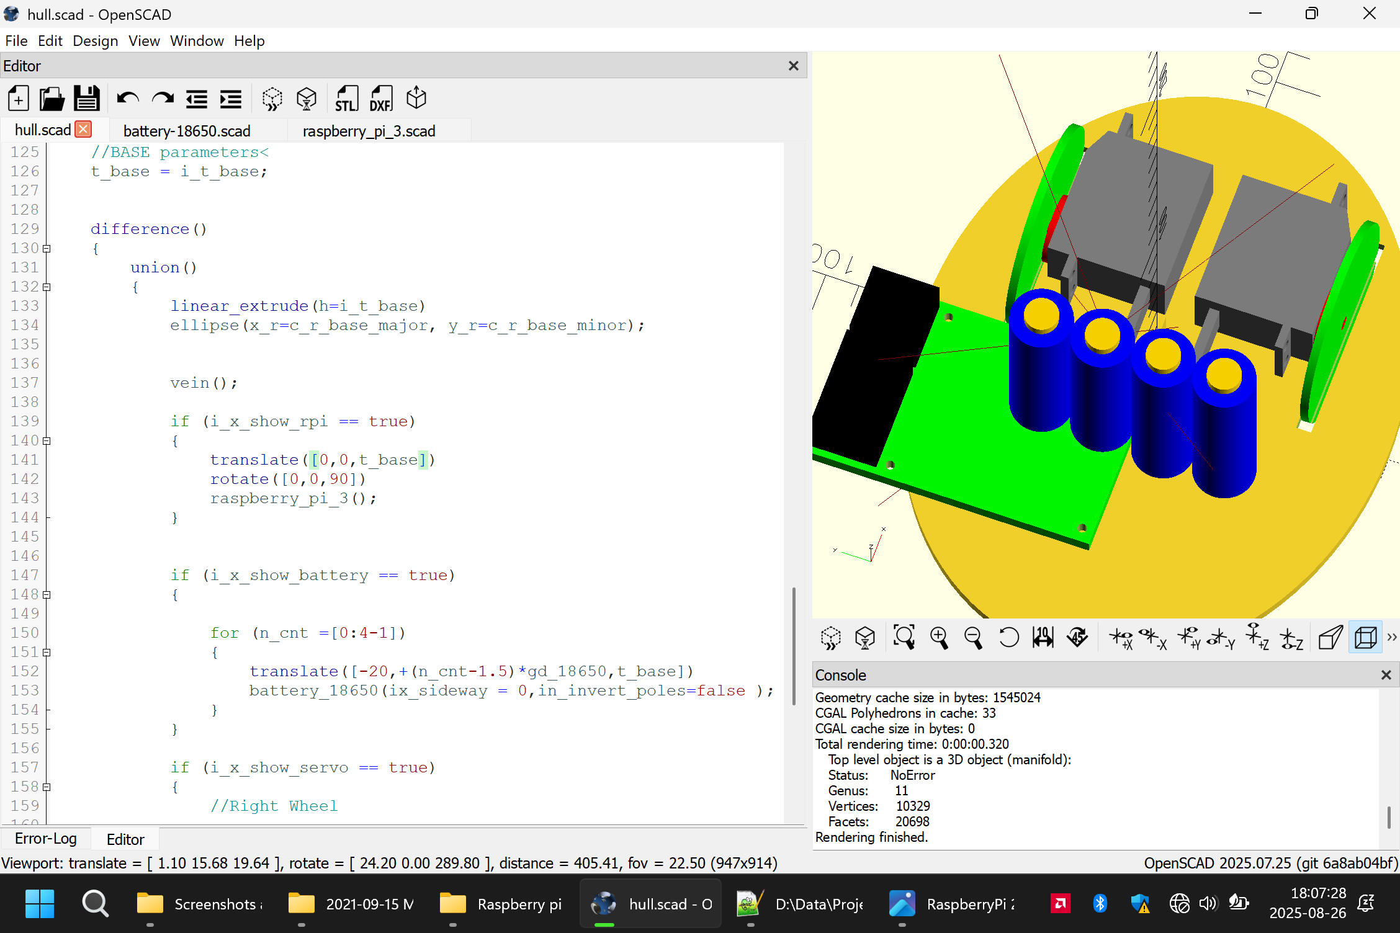
Images/Screenshot (3).png
