OrsoEric/robot-ros2-Industrious-Resonance/Images/Screenshot (5).png

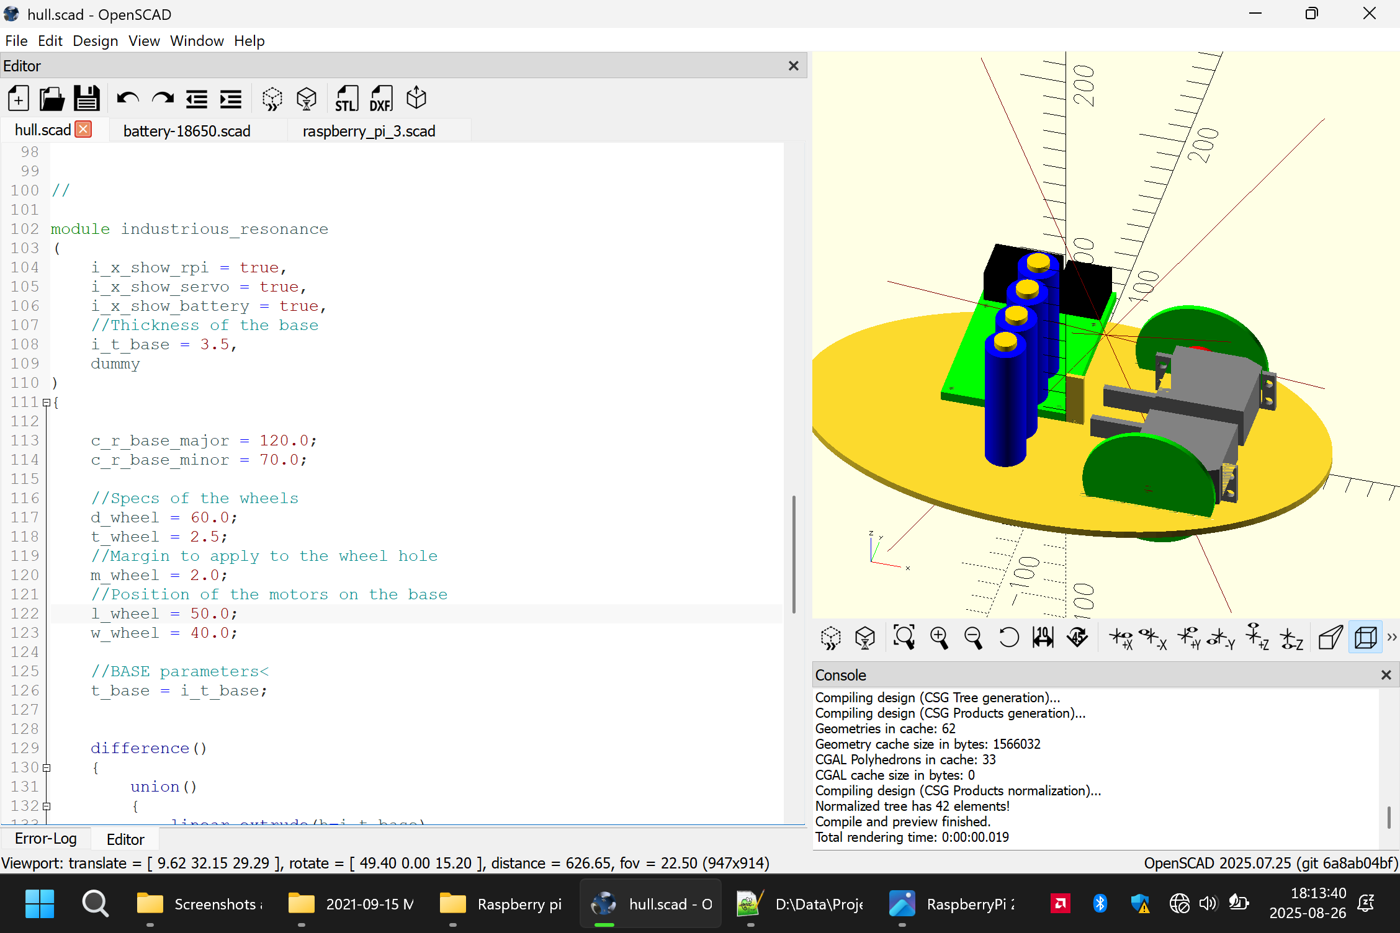
Images/Screenshot (5).png
