OrsoEric/robot-ros2-Industrious-Resonance/Images/Screenshot (37).png

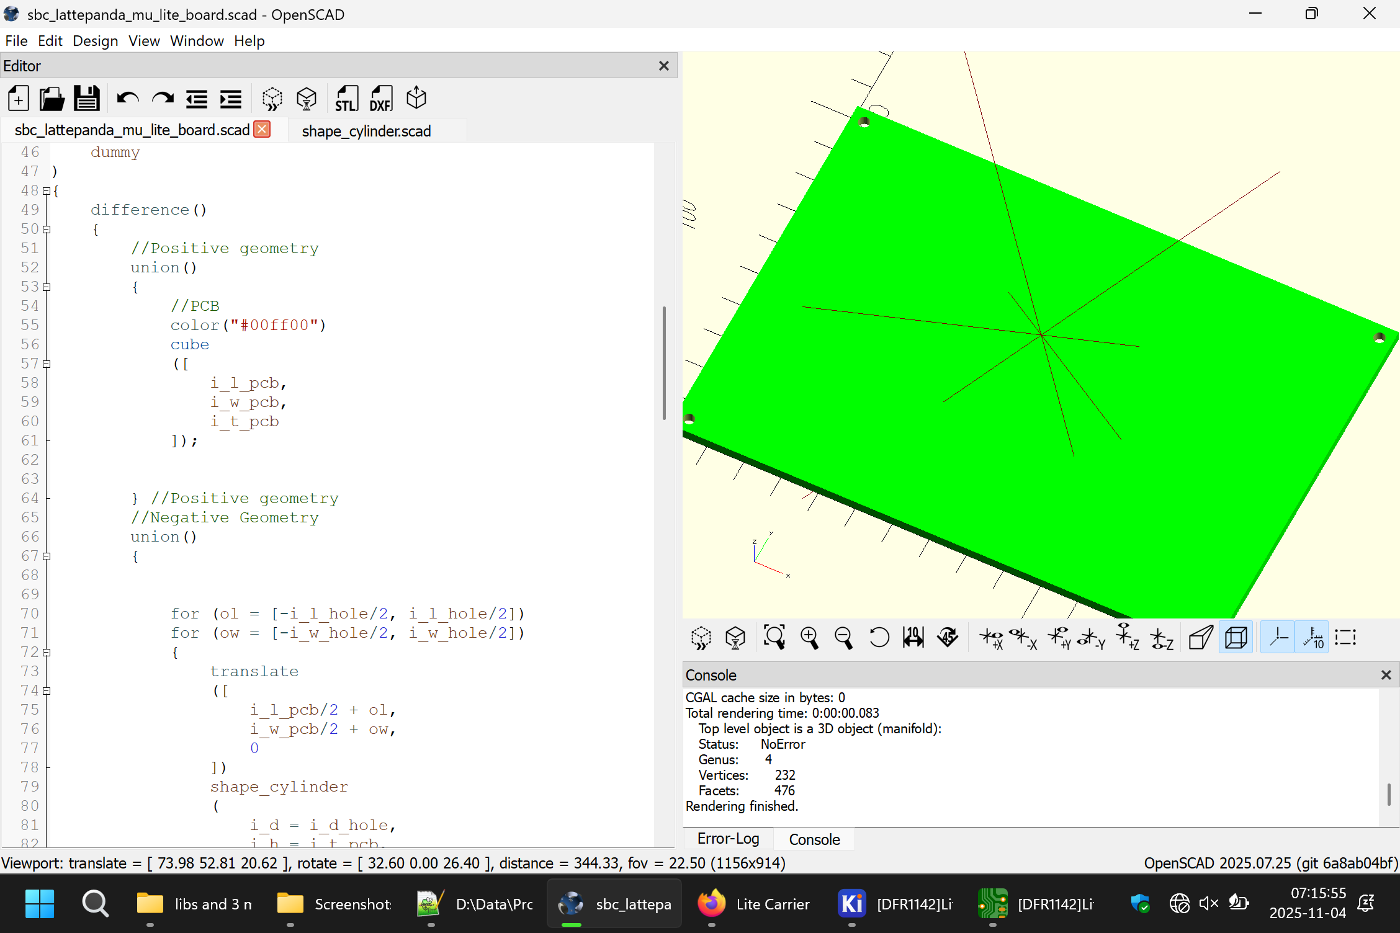
Images/Screenshot (37).png
