OrsoEric/robot-ros2-Industrious-Resonance/Images/Screenshot (38).png

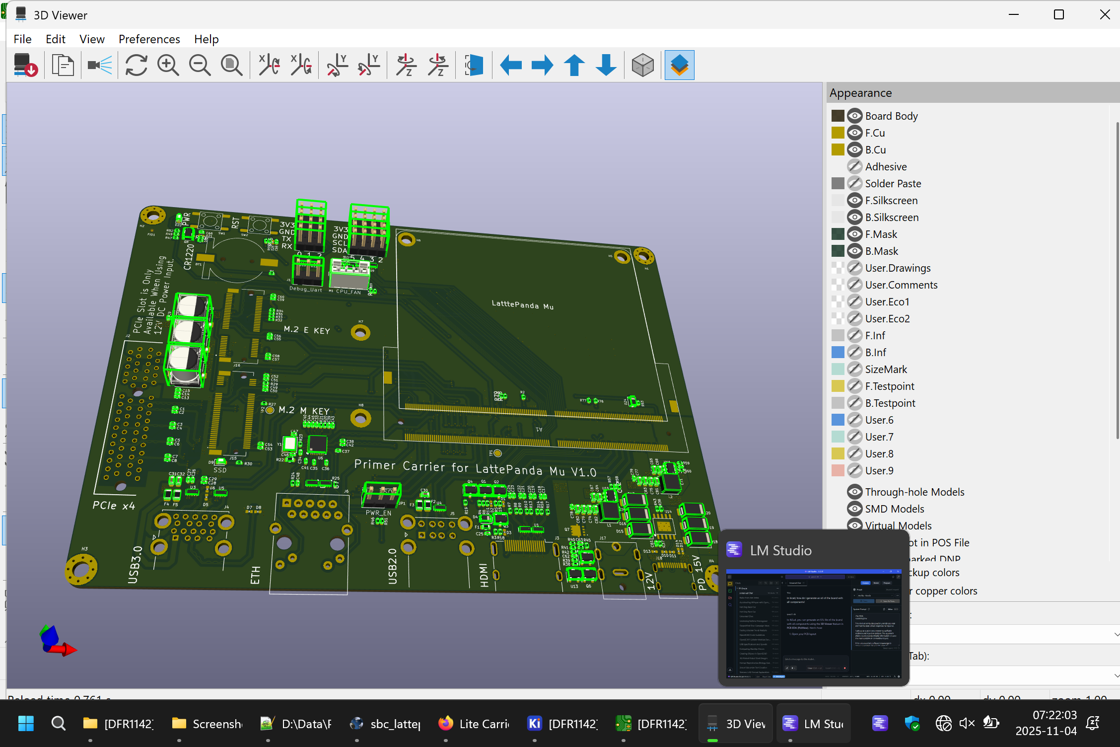
Images/Screenshot (38).png
