OrsoEric/robot-ros2-Industrious-Resonance/Images/Screenshot (39).png

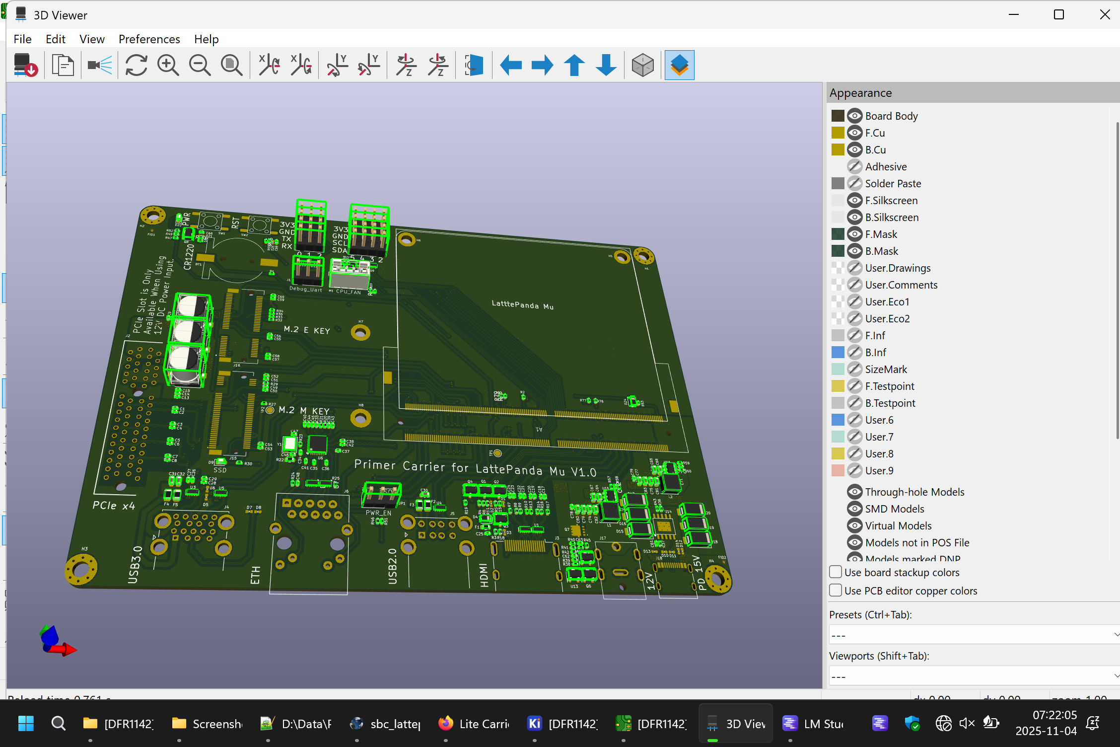
Images/Screenshot (39).png
