OrsoEric/robot-ros2-Industrious-Resonance/Images/Screenshot (40).png

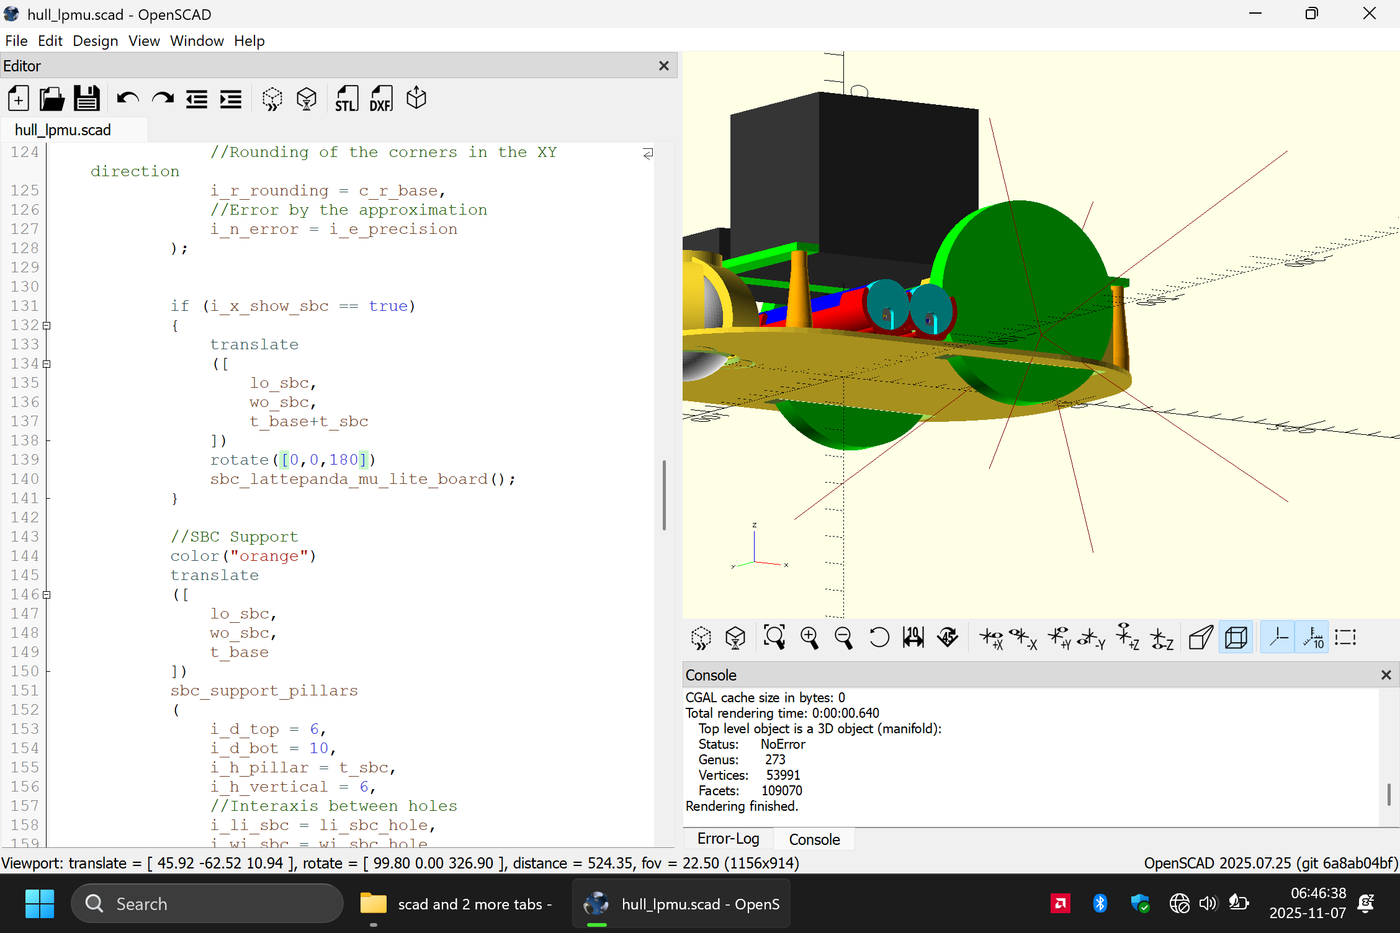
Images/Screenshot (40).png
