OrsoEric/robot-ros2-Industrious-Resonance/Images/Screenshot (43).png

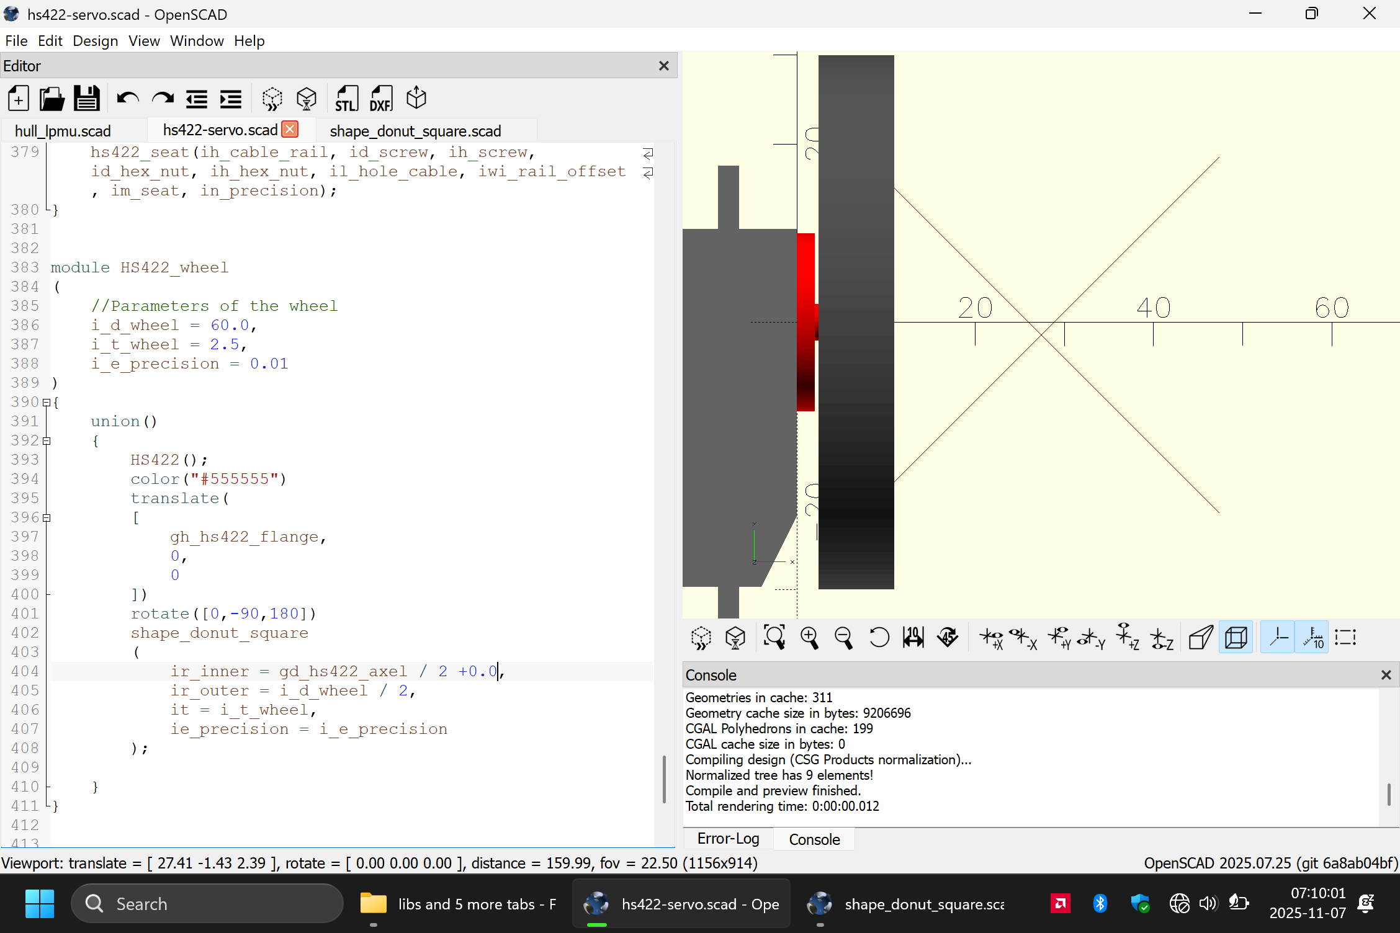
Images/Screenshot (43).png
