OrsoEric/robot-ros2-Industrious-Resonance/Images/Screenshot (44).png

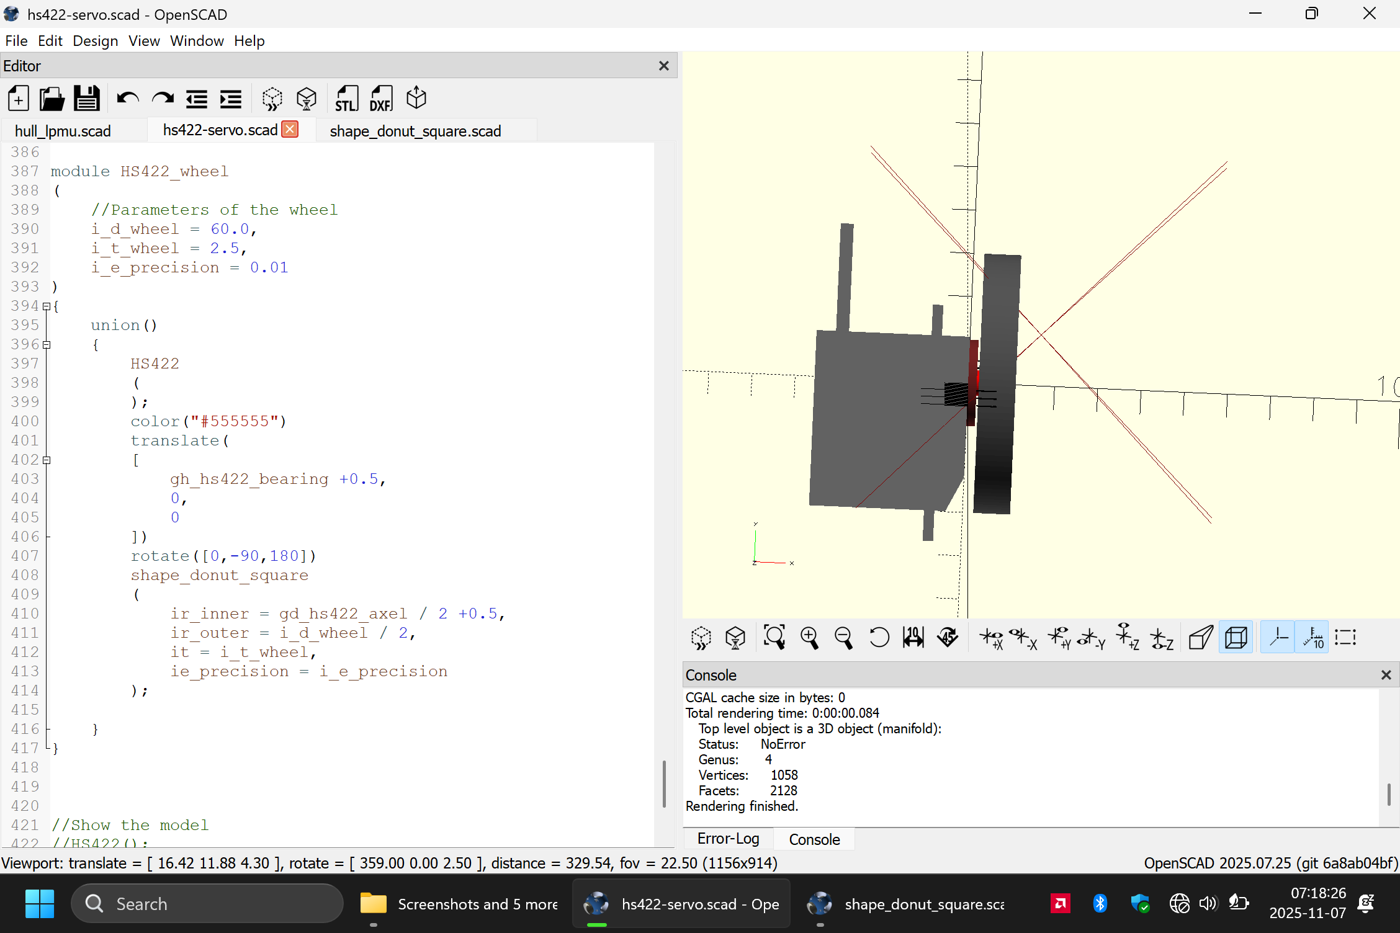
Images/Screenshot (44).png
