OrsoEric/robot-ros2-Industrious-Resonance/Images/Screenshot (45).png

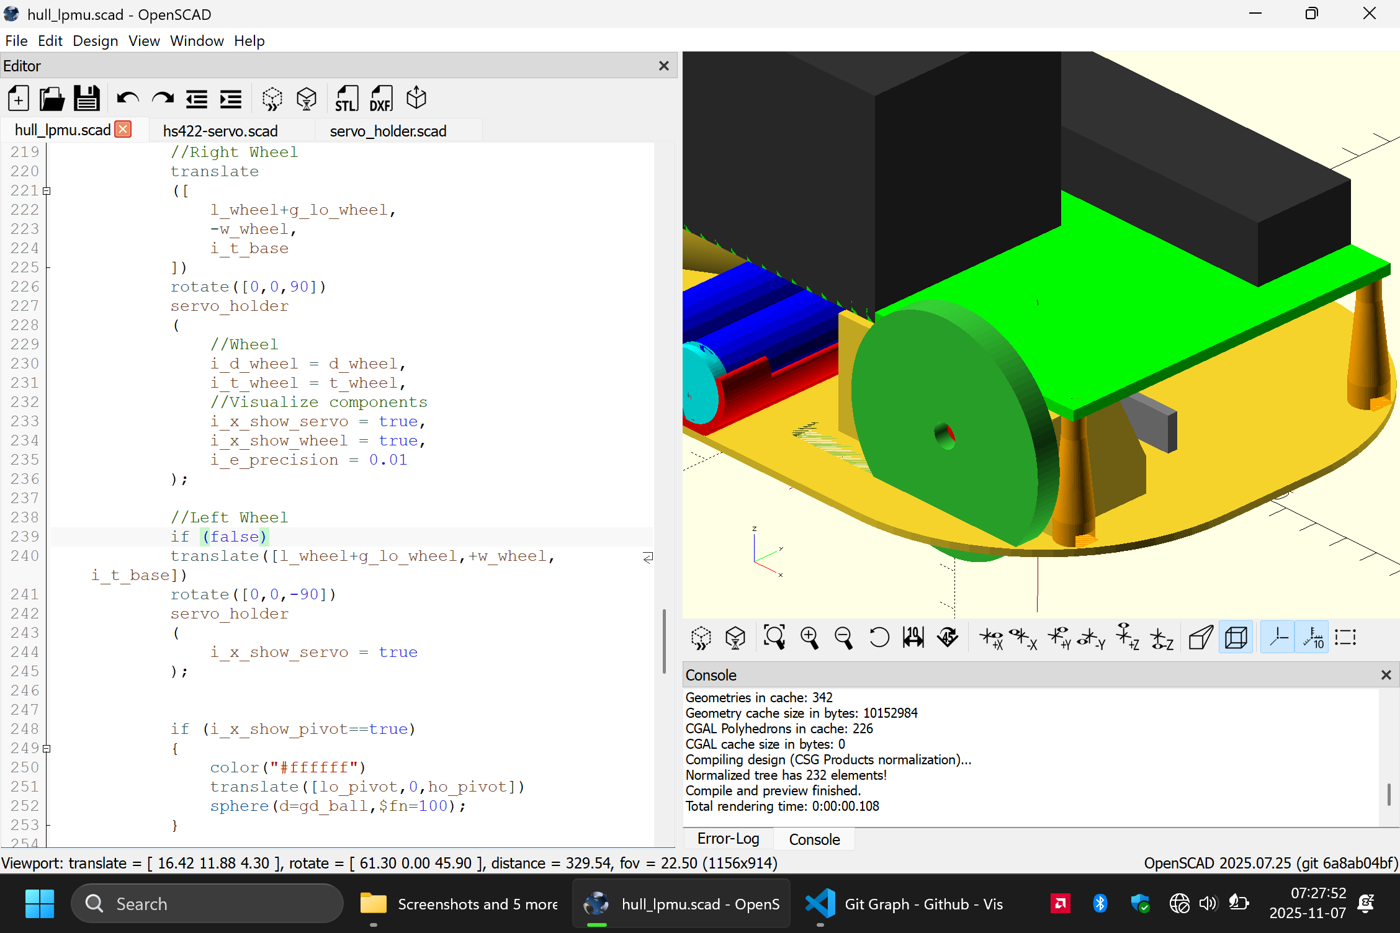
Images/Screenshot (45).png
