OrsoEric/robot-ros2-Industrious-Resonance/Images/Screenshot (46).png

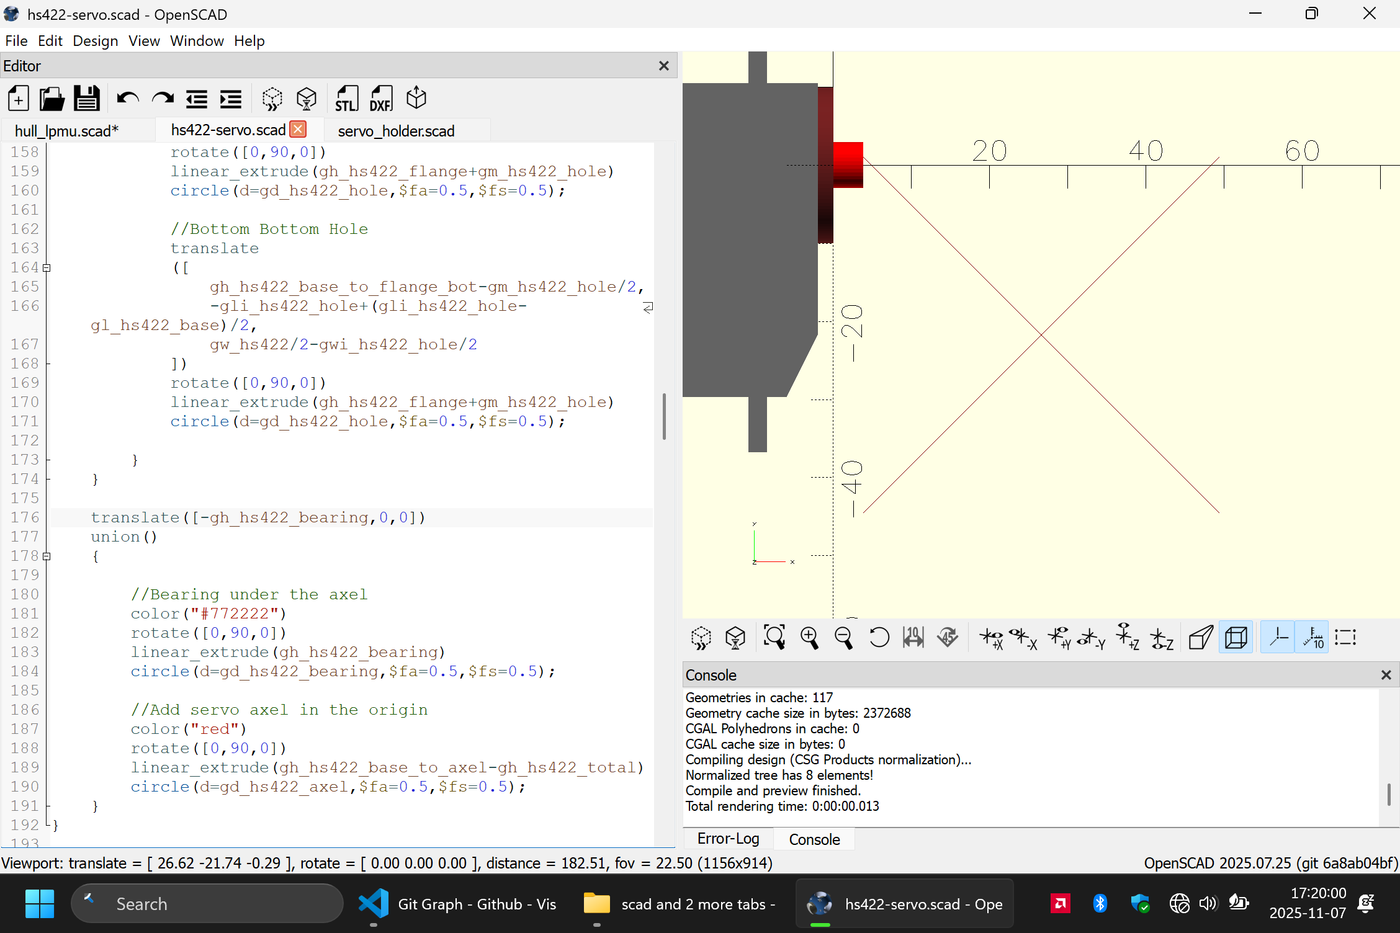
Images/Screenshot (46).png
