OrsoEric/robot-ros2-Industrious-Resonance/Images/Screenshot (47).png

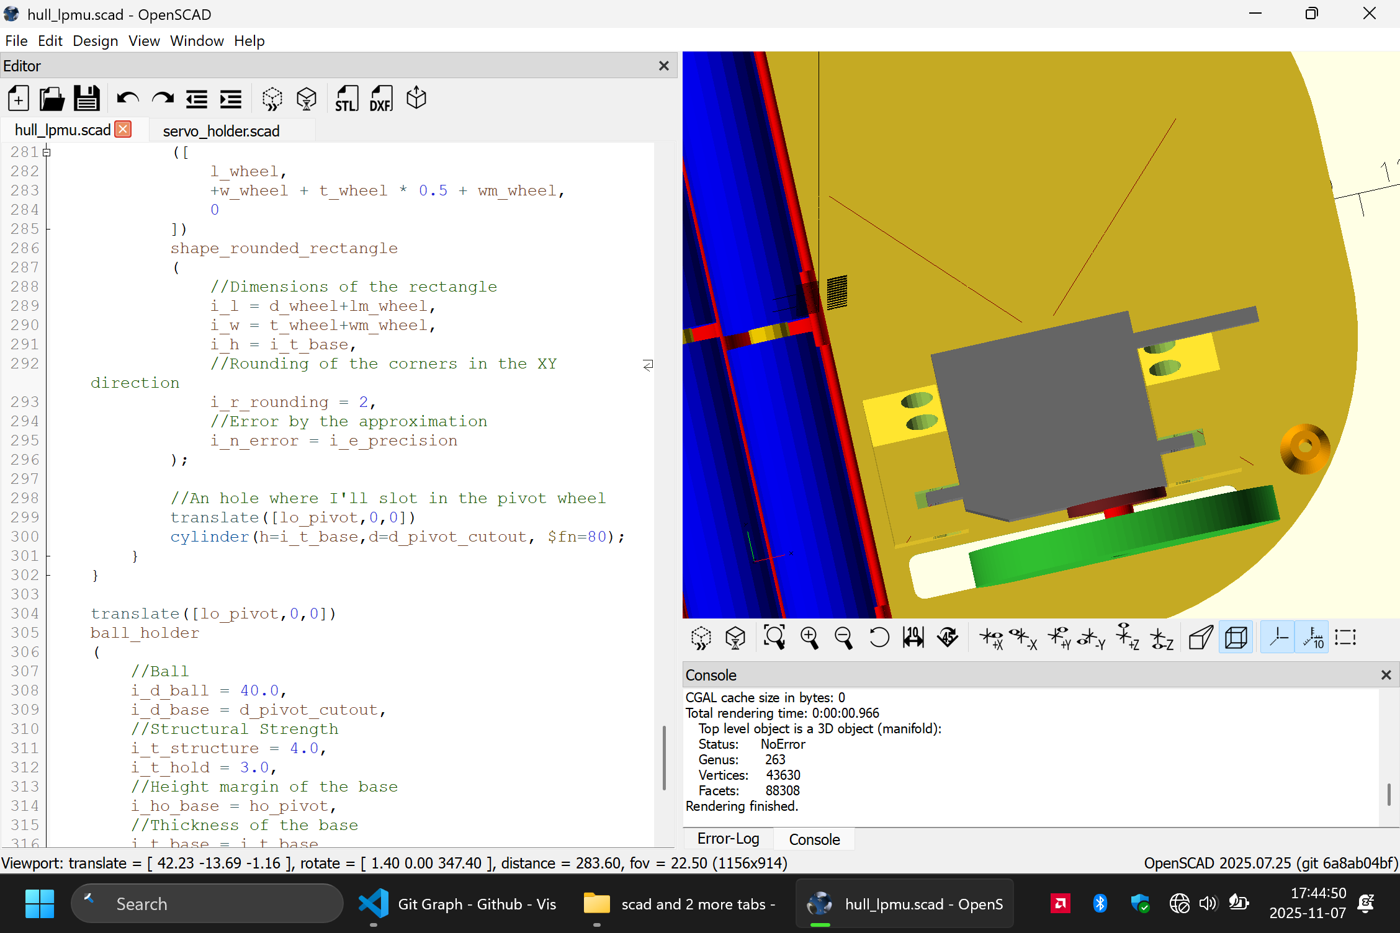
Images/Screenshot (47).png
