OrsoEric/robot-ros2-Industrious-Resonance/Images/Screenshot (50).png

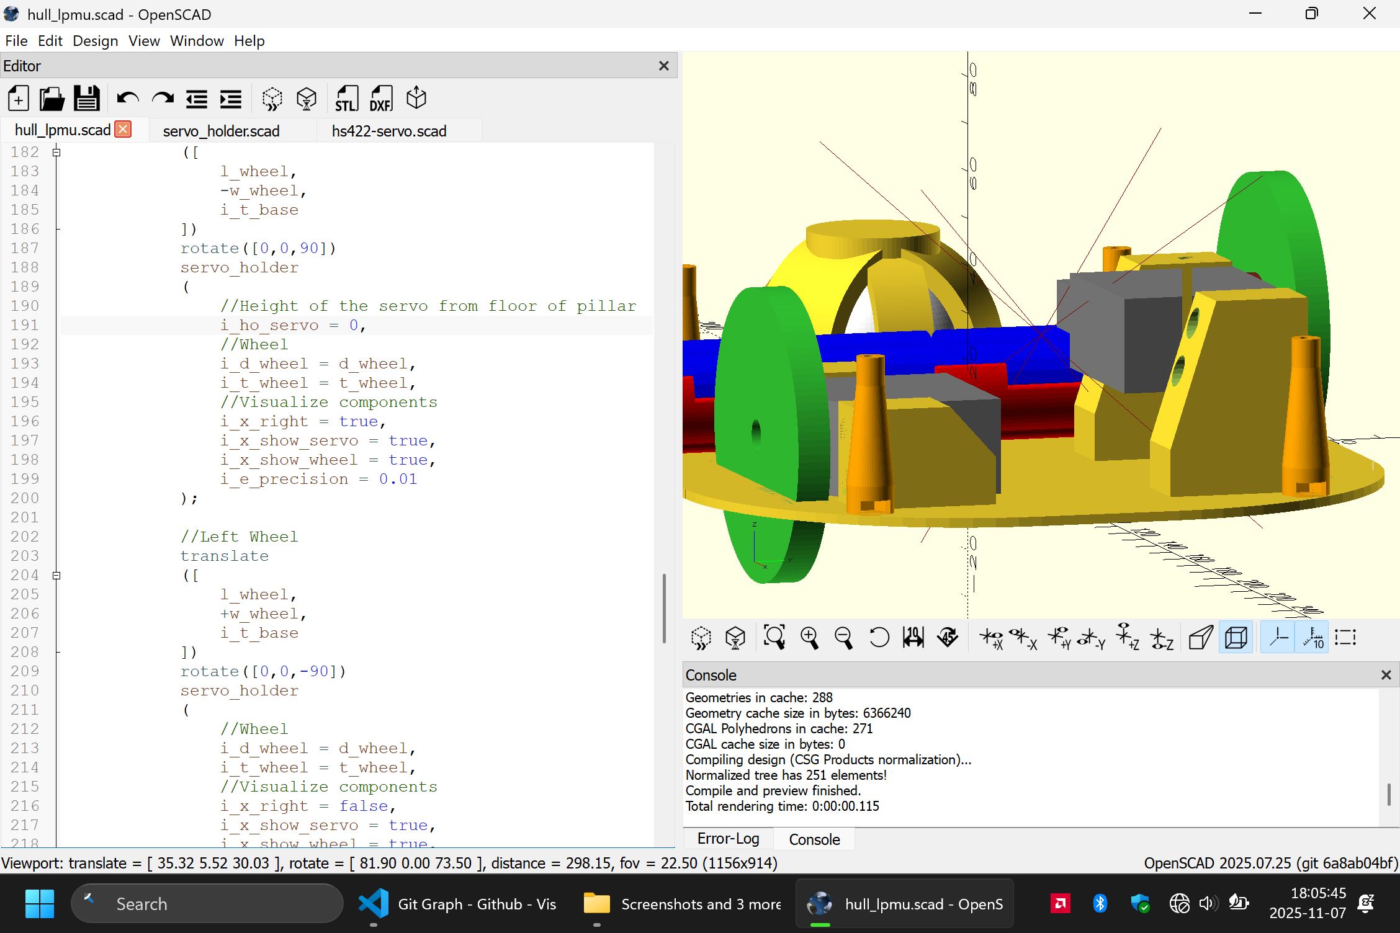
Images/Screenshot (50).png
