OrsoEric/robot-ros2-Industrious-Resonance/Images/Screenshot (51).png

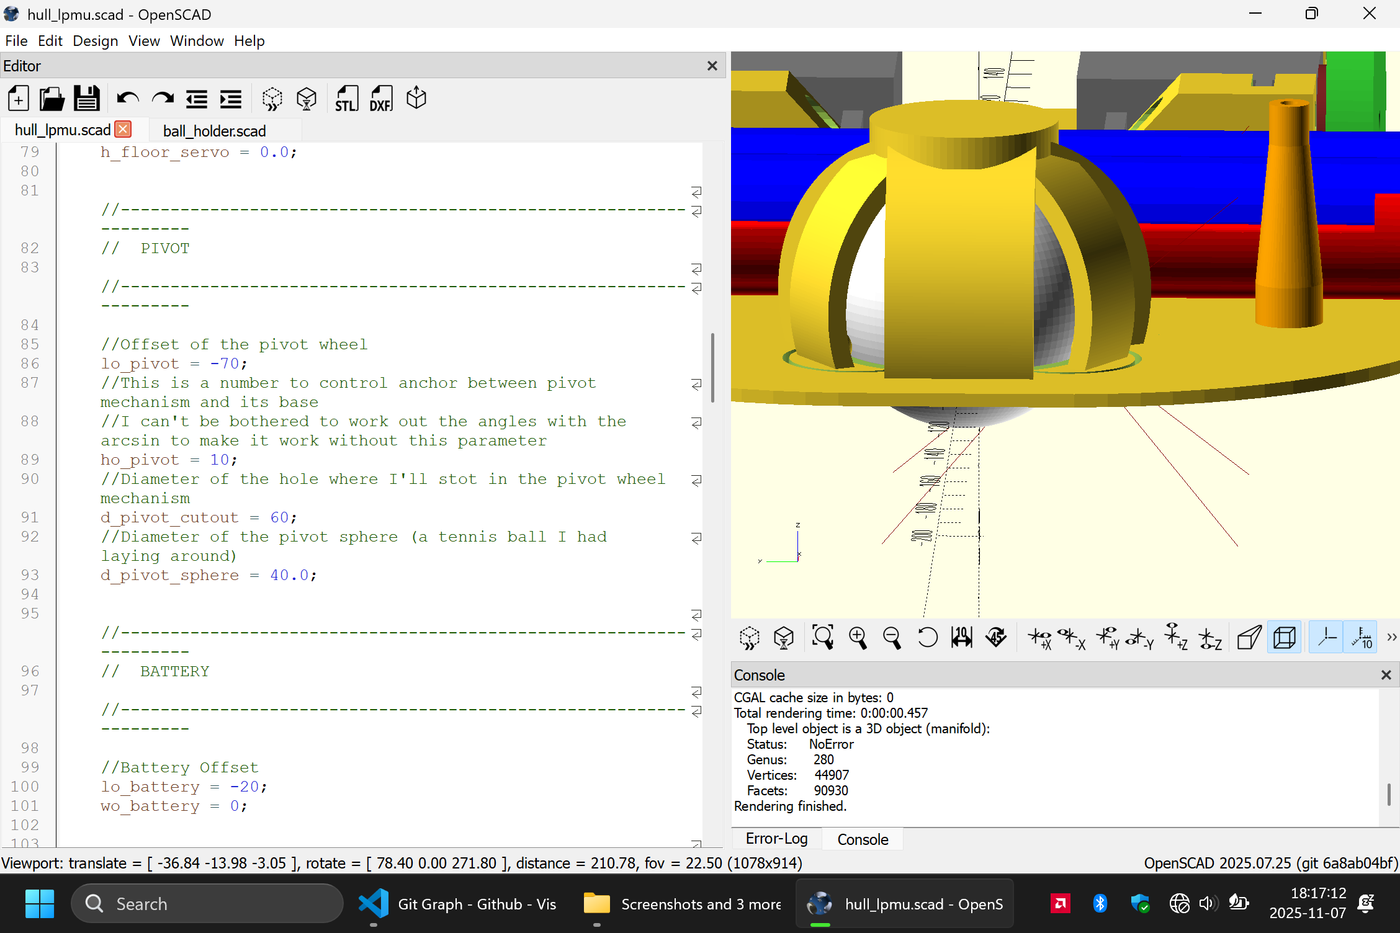
Images/Screenshot (51).png
